HoldenLab/microscope-incubation-box/Individual_parts/R2_door.dxf

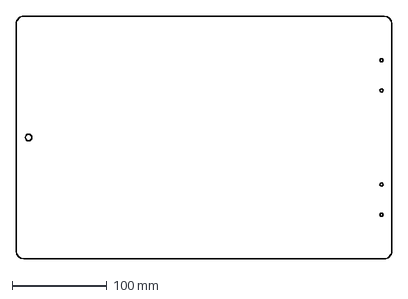
[picture p3: CAD file, 2018-10-10]
Individual_parts/R2_door.dxf
396.0 x 256.0 mm
