HoldenLab/microscope-incubation-box/Individual_parts/PDFs/F6_top_door_hinges_2spacers.pdf

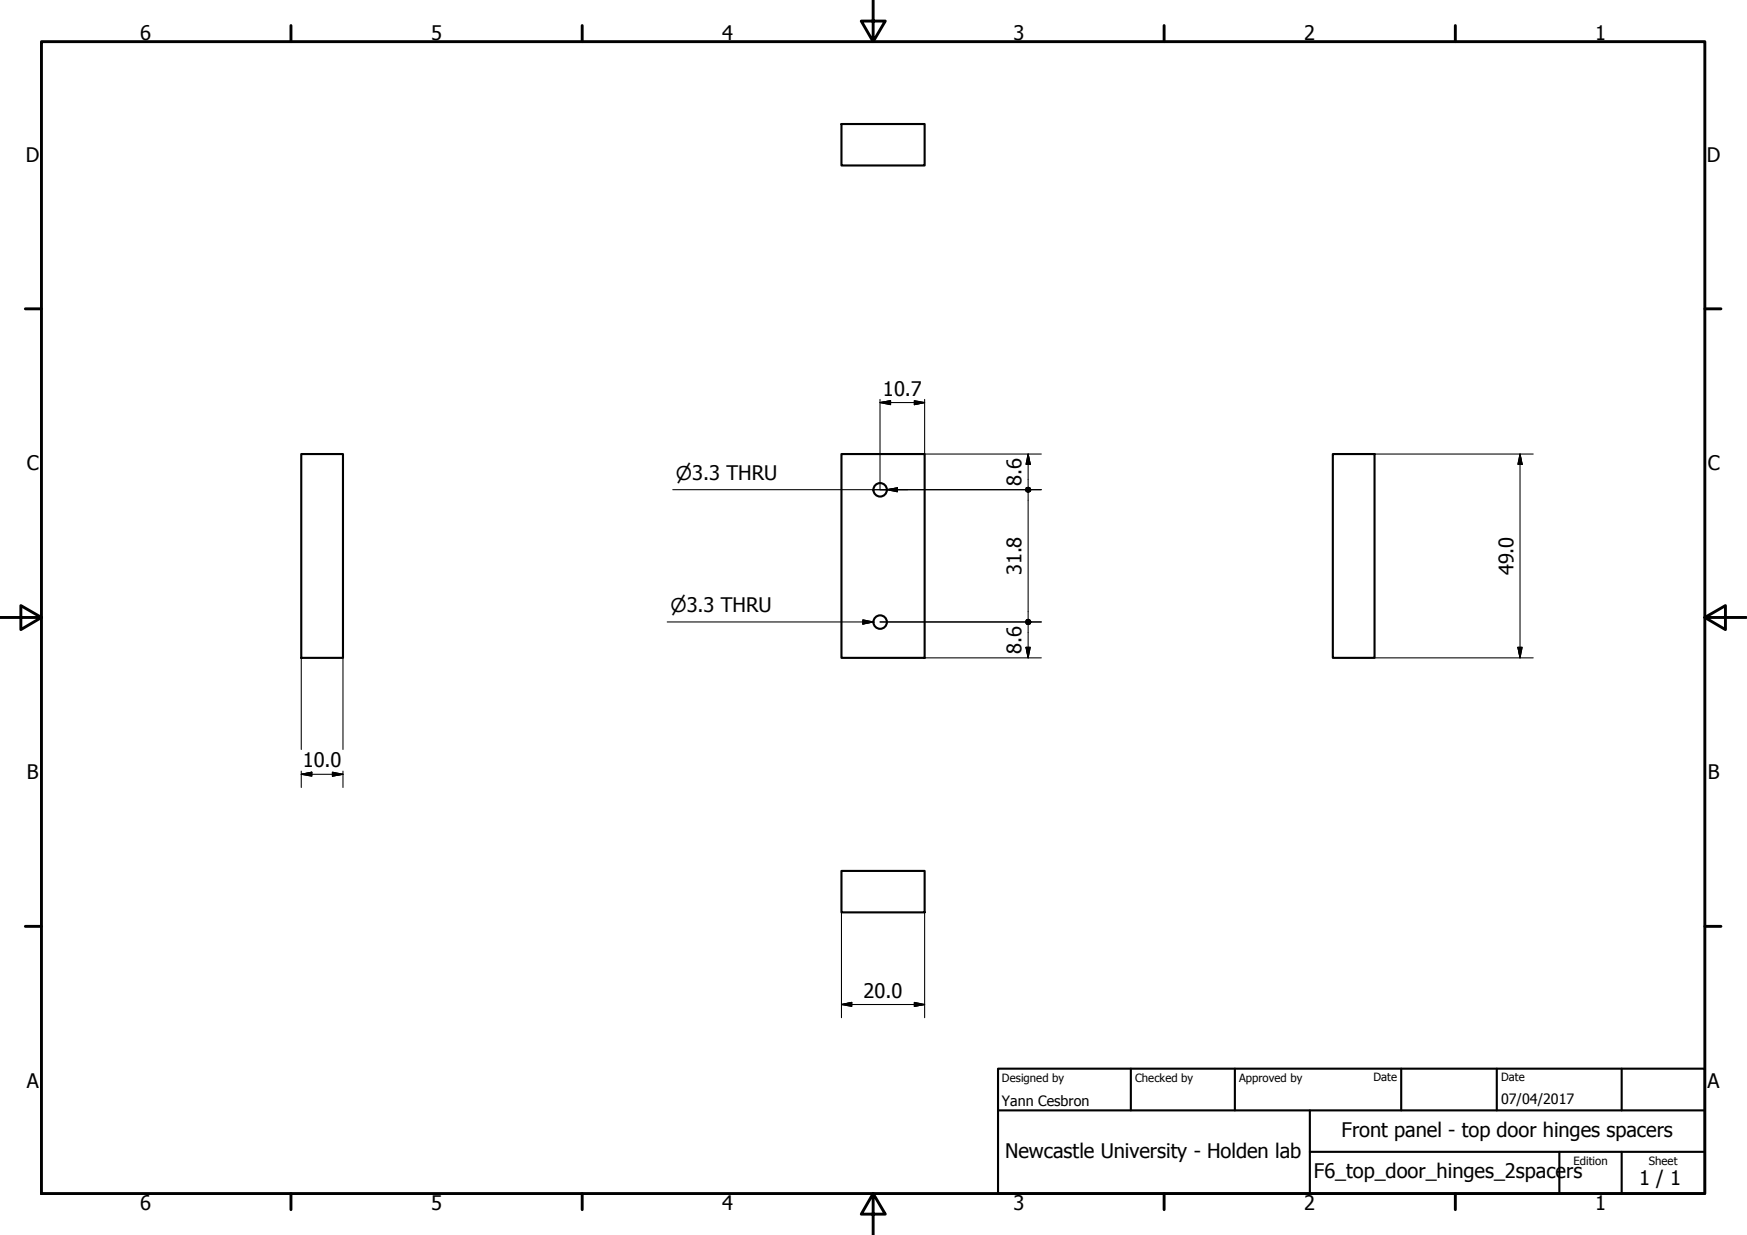
[picture p10: page 1]
F6_top_door_hinges_2spacers; Yann Cesbron; Designed by; Checked by; Approved by; Date; Edition; Sheet; P3.3 THRU

Front panel - top door hinges spacers

Newcastle University - Holden lab
