HoldenLab/microscope-incubation-box/Individual_parts/PDFs/L8_door_magnet_flange.pdf

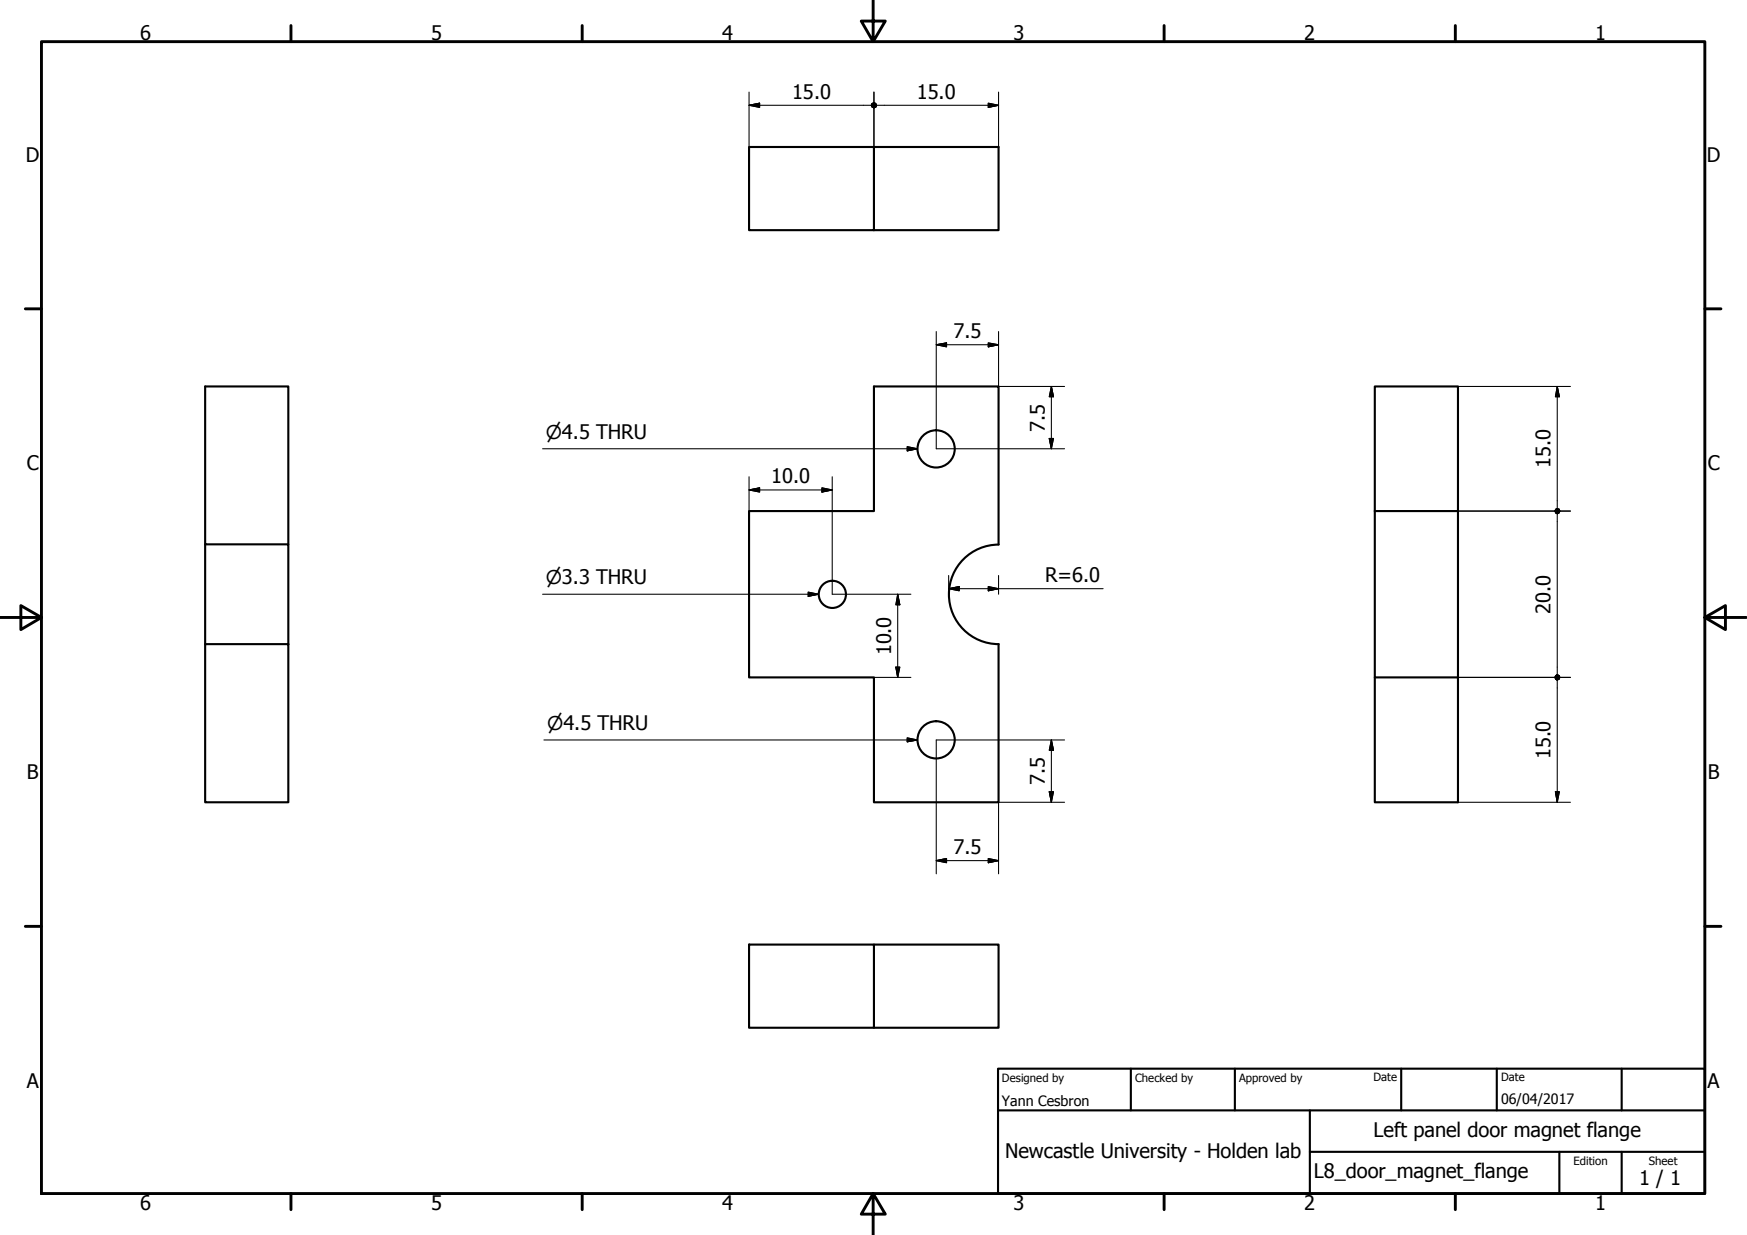
[picture p11: page 1]
L8_door_magnet_flange; Yann Cesbron; Designed by; Checked by; Approved by; Date; Edition; Sheet; P4.5 THRU; P3.3 THRU

Left panel door magnet flange

Newcastle University - Holden lab
