HoldenLab/microscope-incubation-box/Individual_parts/PDFs/R3_CRISP_flange.pdf

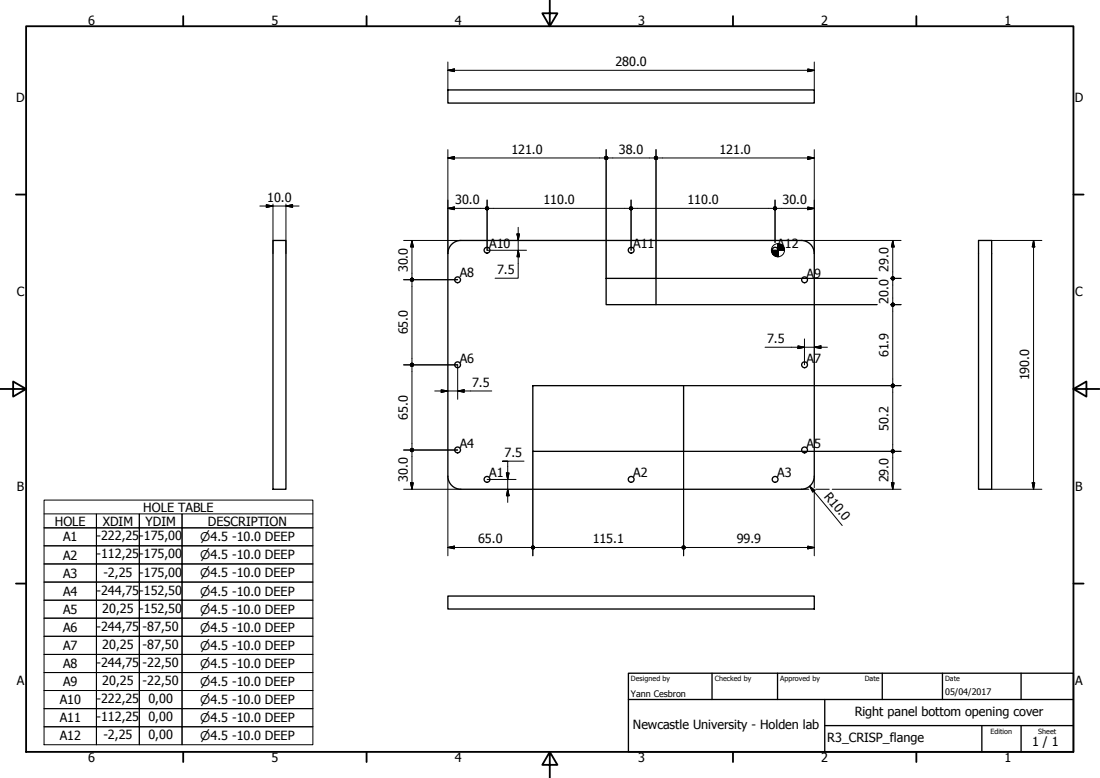
[picture p12: page 1]
R3_CRISP_flange; Yann Cesbron; Designed by; Checked by; Approved by; Date; Edition; Sheet; HOLE TABLE; HOLE; XDIM YDIM; DESCRIPTION; P4.5 -10.0 DEEP

Right panel bottom opening cover

Newcastle University - Holden lab
