HoldenLab/microscope-incubation-box/Individual_parts/PDFs/R8_door_magnet_flange.pdf

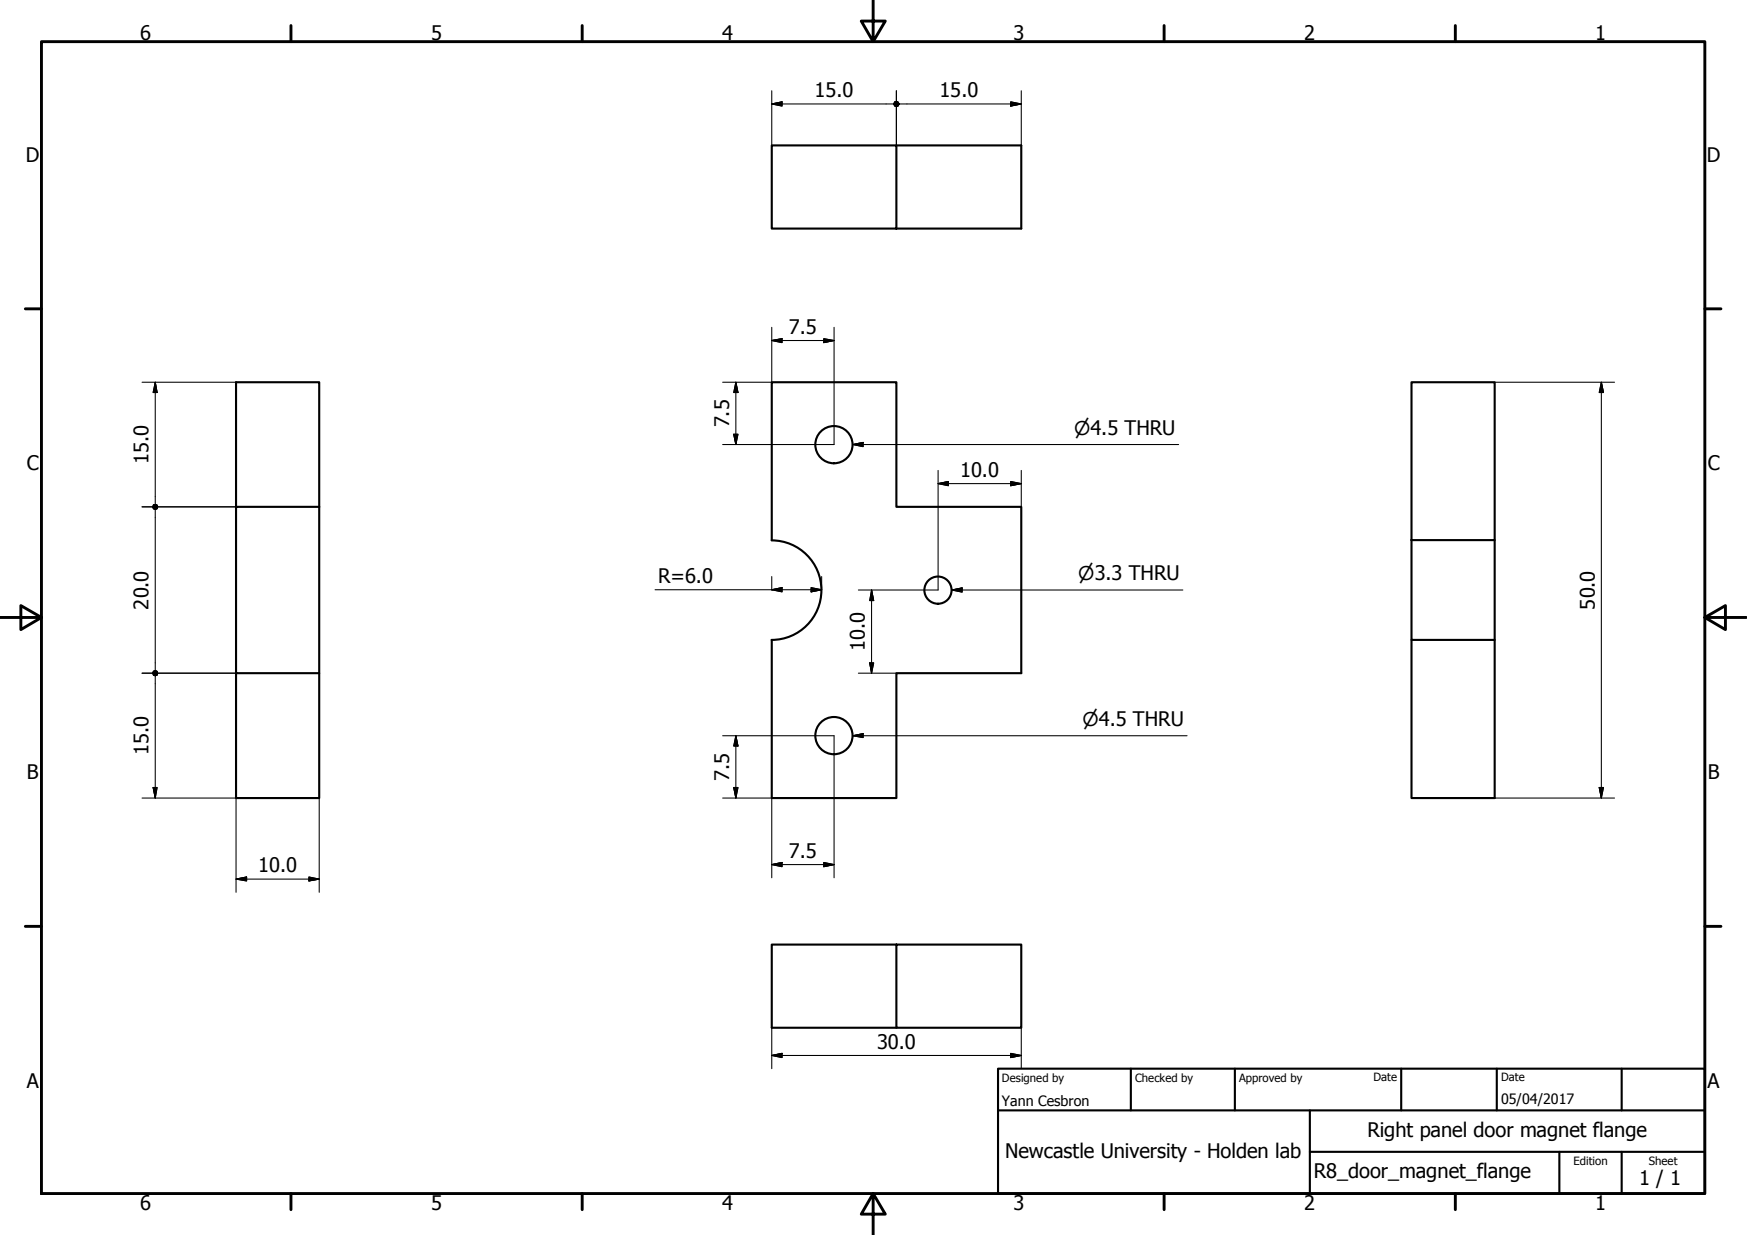
[picture p13: page 1]
R8_door_magnet_flange; Yann Cesbron; Designed by; Checked by; Approved by; Date; Edition; Sheet; P4.5 THRU; P3.3 THRU

Right panel door magnet flange

Newcastle University - Holden lab
