HoldenLab/microscope-incubation-box/Individual_parts/PDFs/T3_flanges.pdf

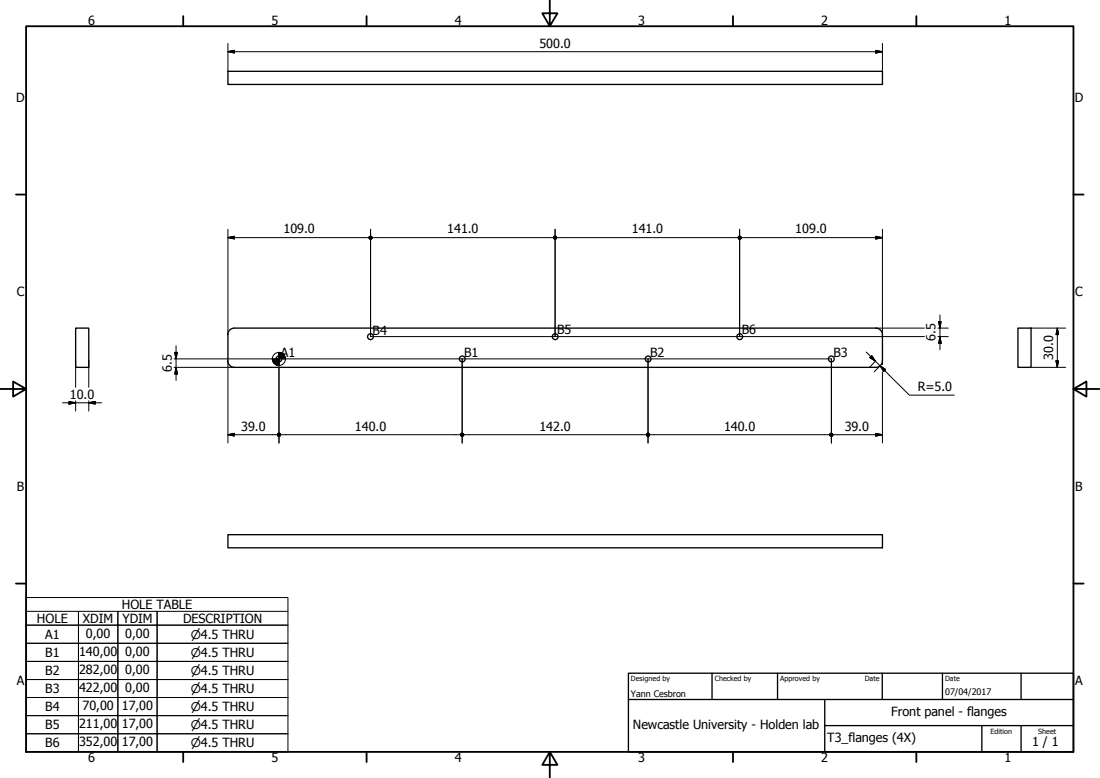
[picture p14: page 1]
T3_flanges (4X); Yann Cesbron; Designed by; Checked by; Approved by; Date; Edition; Sheet; HOLE TABLE; HOLE; XDIM YDIM; DESCRIPTION; P4.5 THRU

Front panel - flanges

Newcastle University - Holden lab
