HoldenLab/microscope-incubation-box/Individual_parts/PDFs/Missing_holes/L1_main.pdf

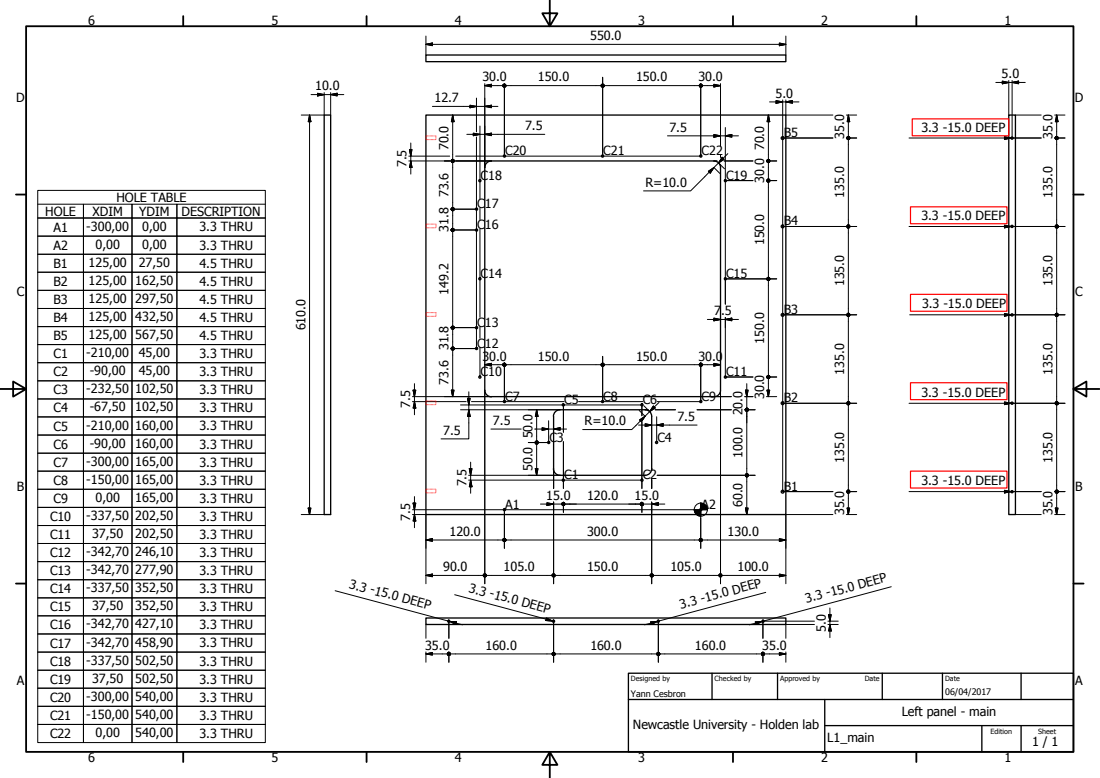
[picture p15: page 1]

HOLE XDIM YDIM DESCRIPTION

Newcastle University - Holden lab
