HoldenLab/microscope-incubation-box/Individual_parts/PDFs/F1_main.pdf

P

P

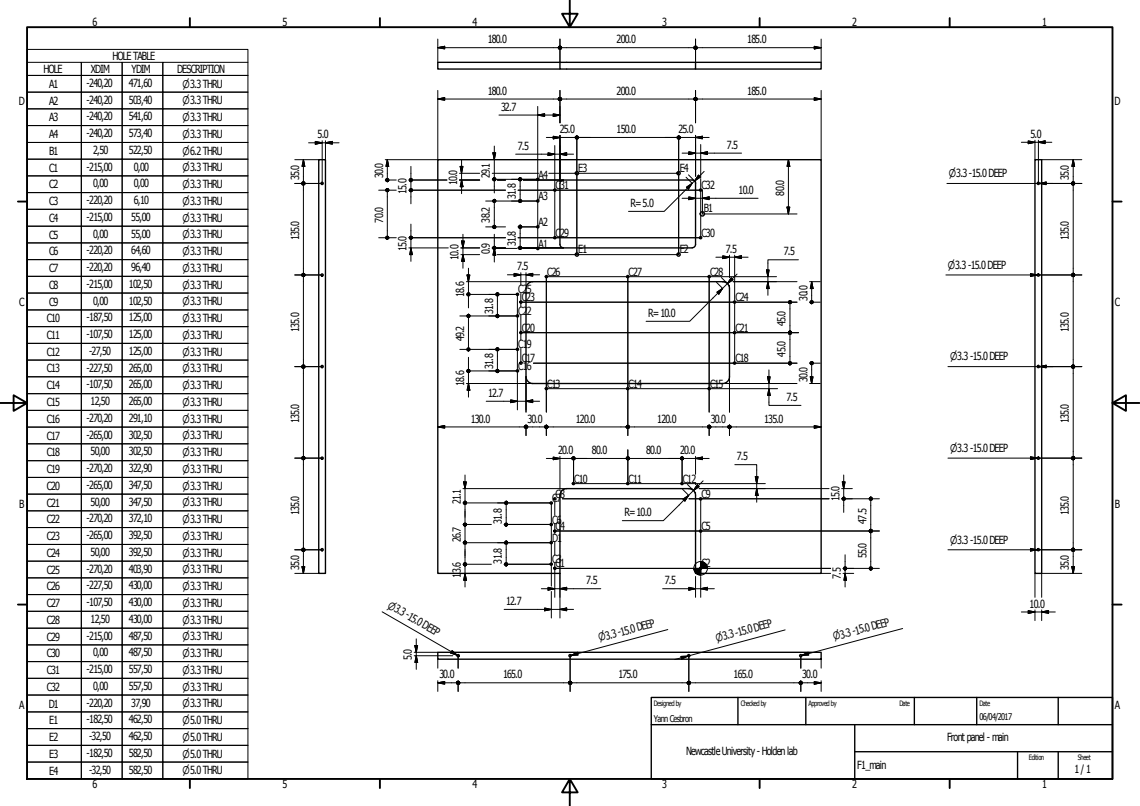
[picture p22: page 1]

E3 | C3 2
C3
