HoldenLab/microscope-incubation-box/Individual_parts/PDFs/F2_top_door.pdf

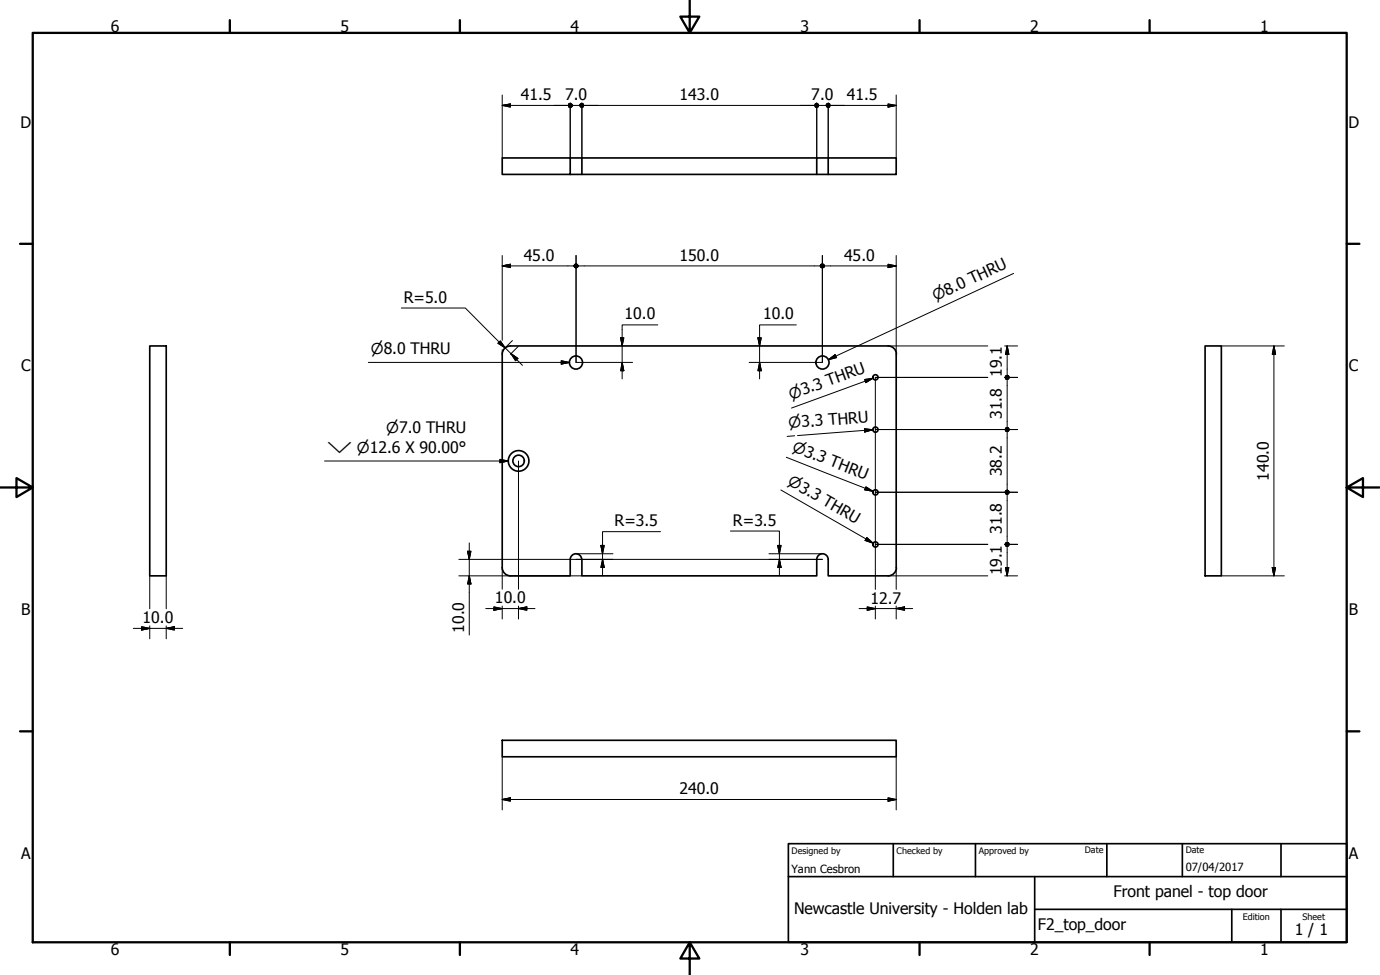
[picture p23: page 1]
F2_top_door; Yann Cesbron; Designed by; Checked by; Approved by; Date; Edition; Sheet; P7.0 THRU Y P12.6 X 90.00°; P8.0 THRU; P3.3 THRU; P3.3 THRU P3.3 THRU

Front panel - top door

Newcastle University - Holden lab
