HoldenLab/microscope-incubation-box/Individual_parts/PDFs/F3_middle_door.pdf

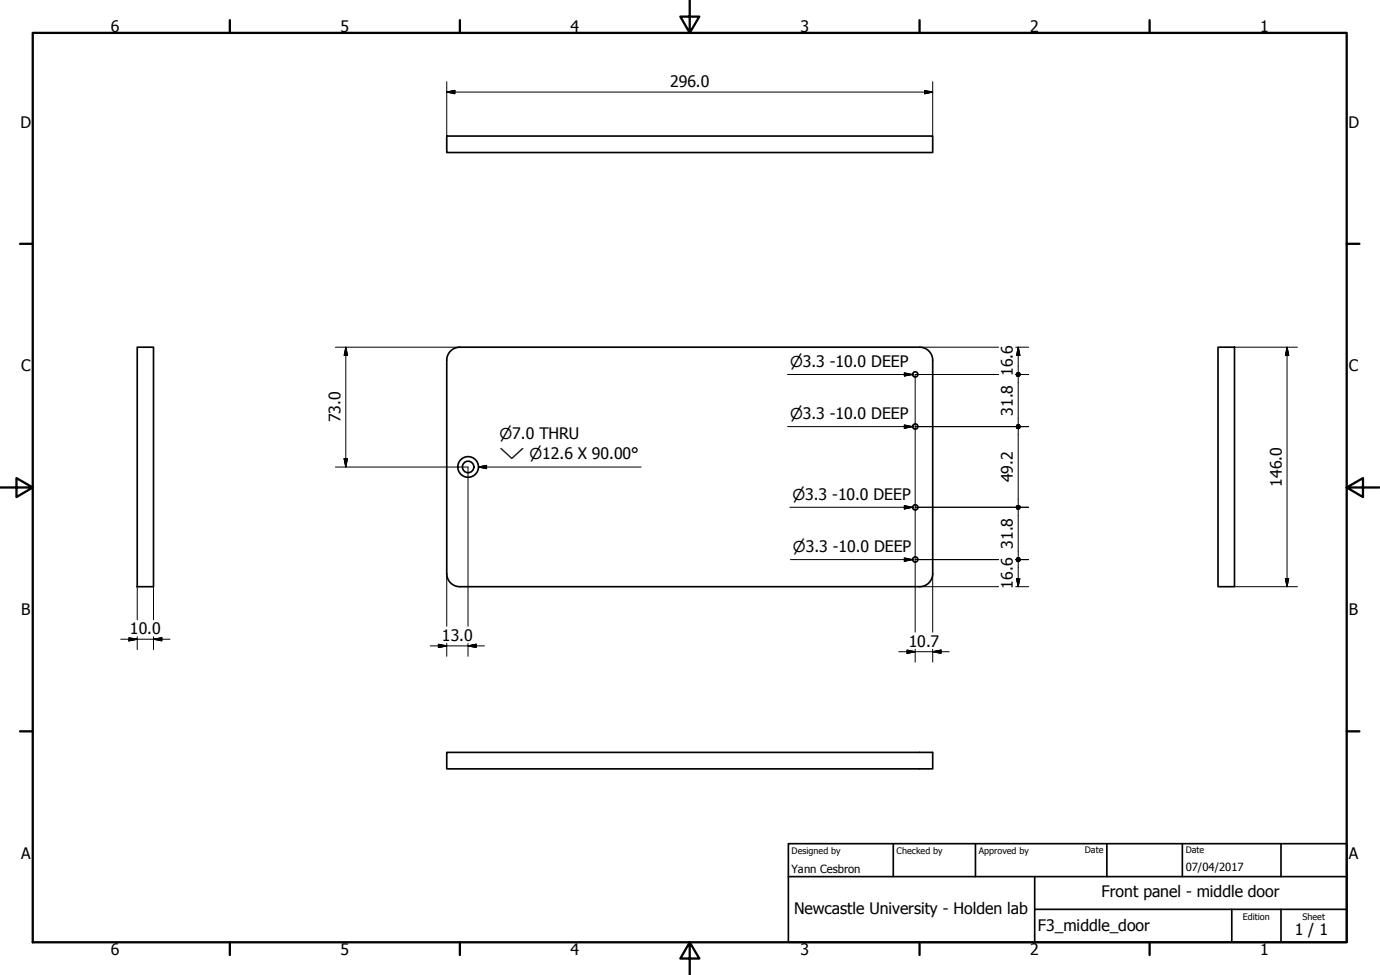
[picture p24: page 1]
F3_middle_door; Yann Cesbron; Designed by; Checked by; Approved by; Date; Edition; Sheet; P3.3 -10.0 DEEP; P7.0 THRU Y P12.6 X 90.00°

Front panel - middle door

Newcastle University - Holden lab
