HoldenLab/microscope-incubation-box/Individual_parts/PDFs/F4_bottom_door.pdf

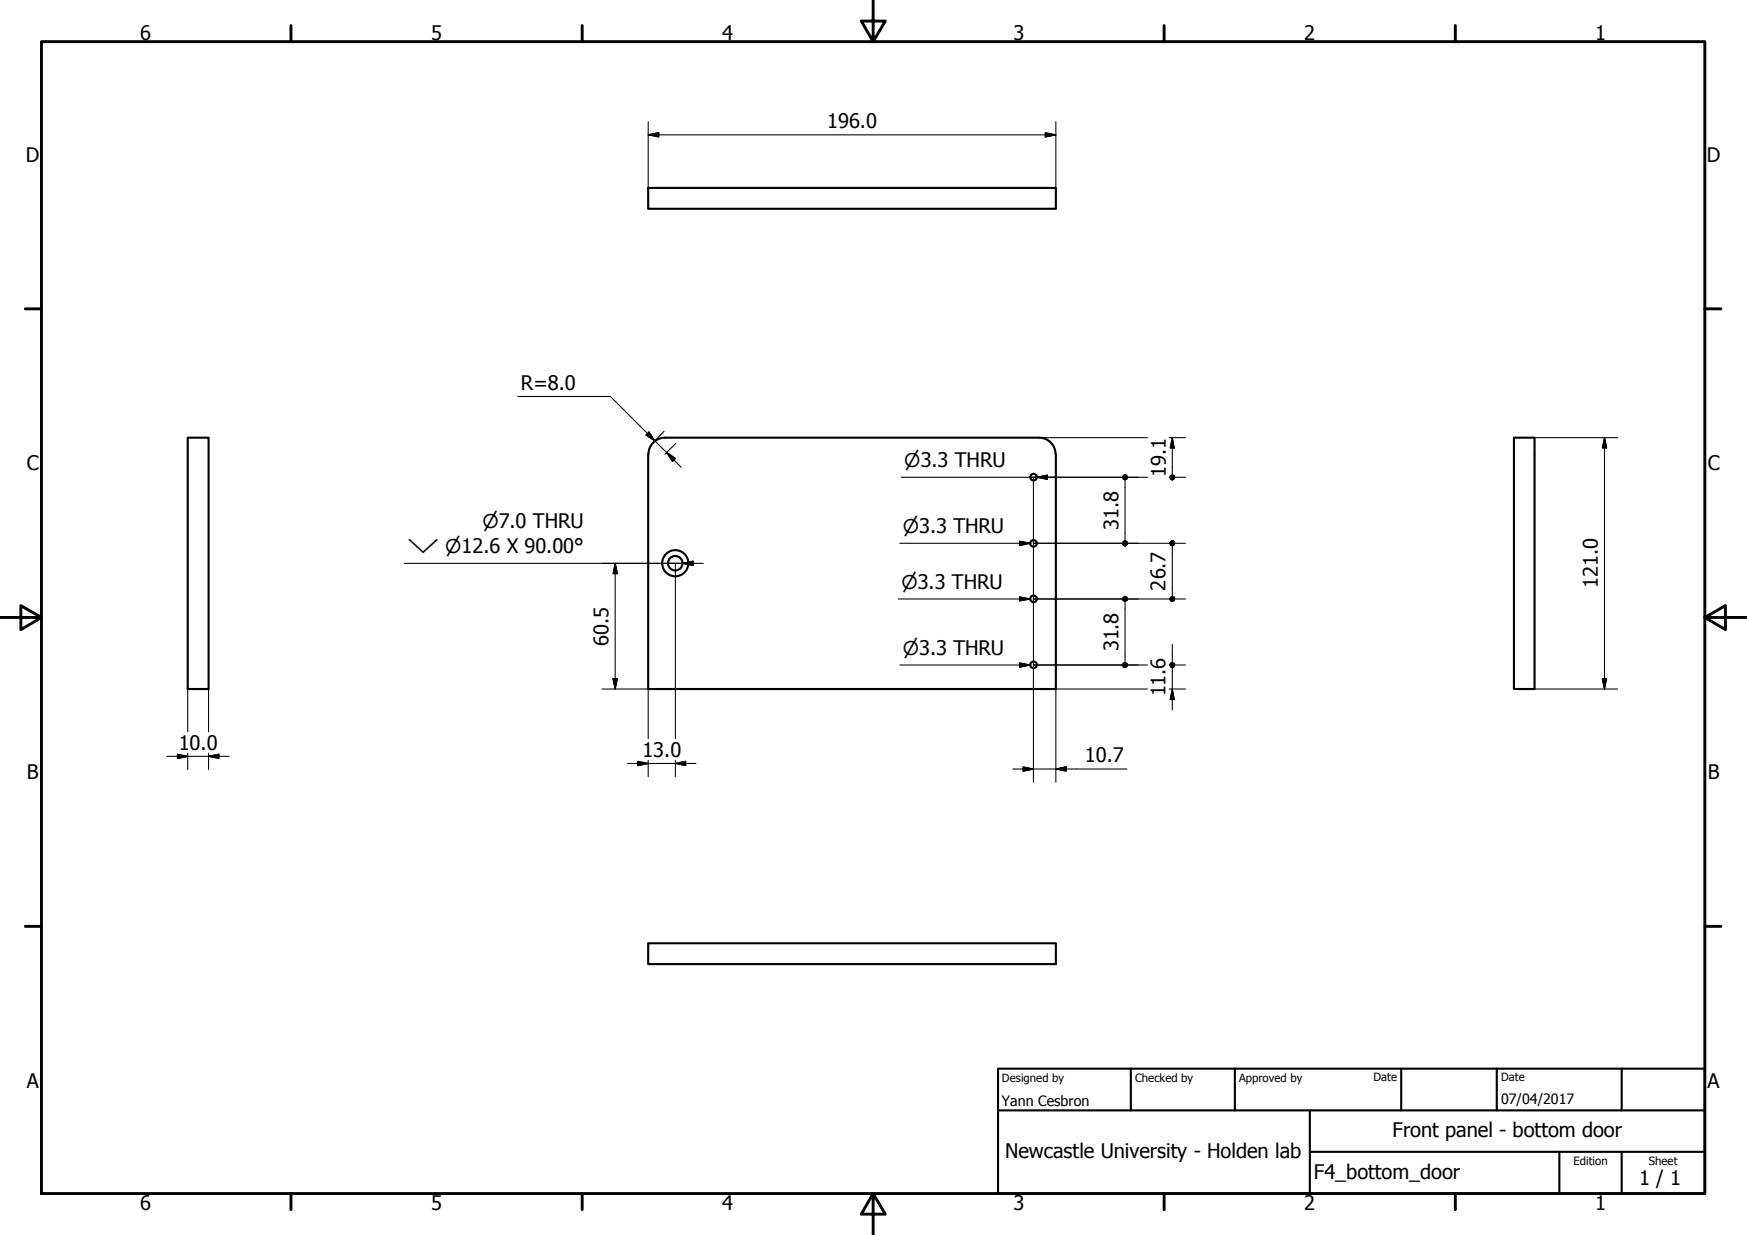
[picture p25: page 1]
F4_bottom_door; Yann Cesbron; Designed by; Checked by; Approved by; Date; Edition; Sheet; P3.3 THRU; P7.0 THRU Y P12.6 X 90.00°

Front panel - bottom door

Newcastle University - Holden lab
