HoldenLab/microscope-incubation-box/Individual_parts/PDFs/F5_top_door_window.pdf

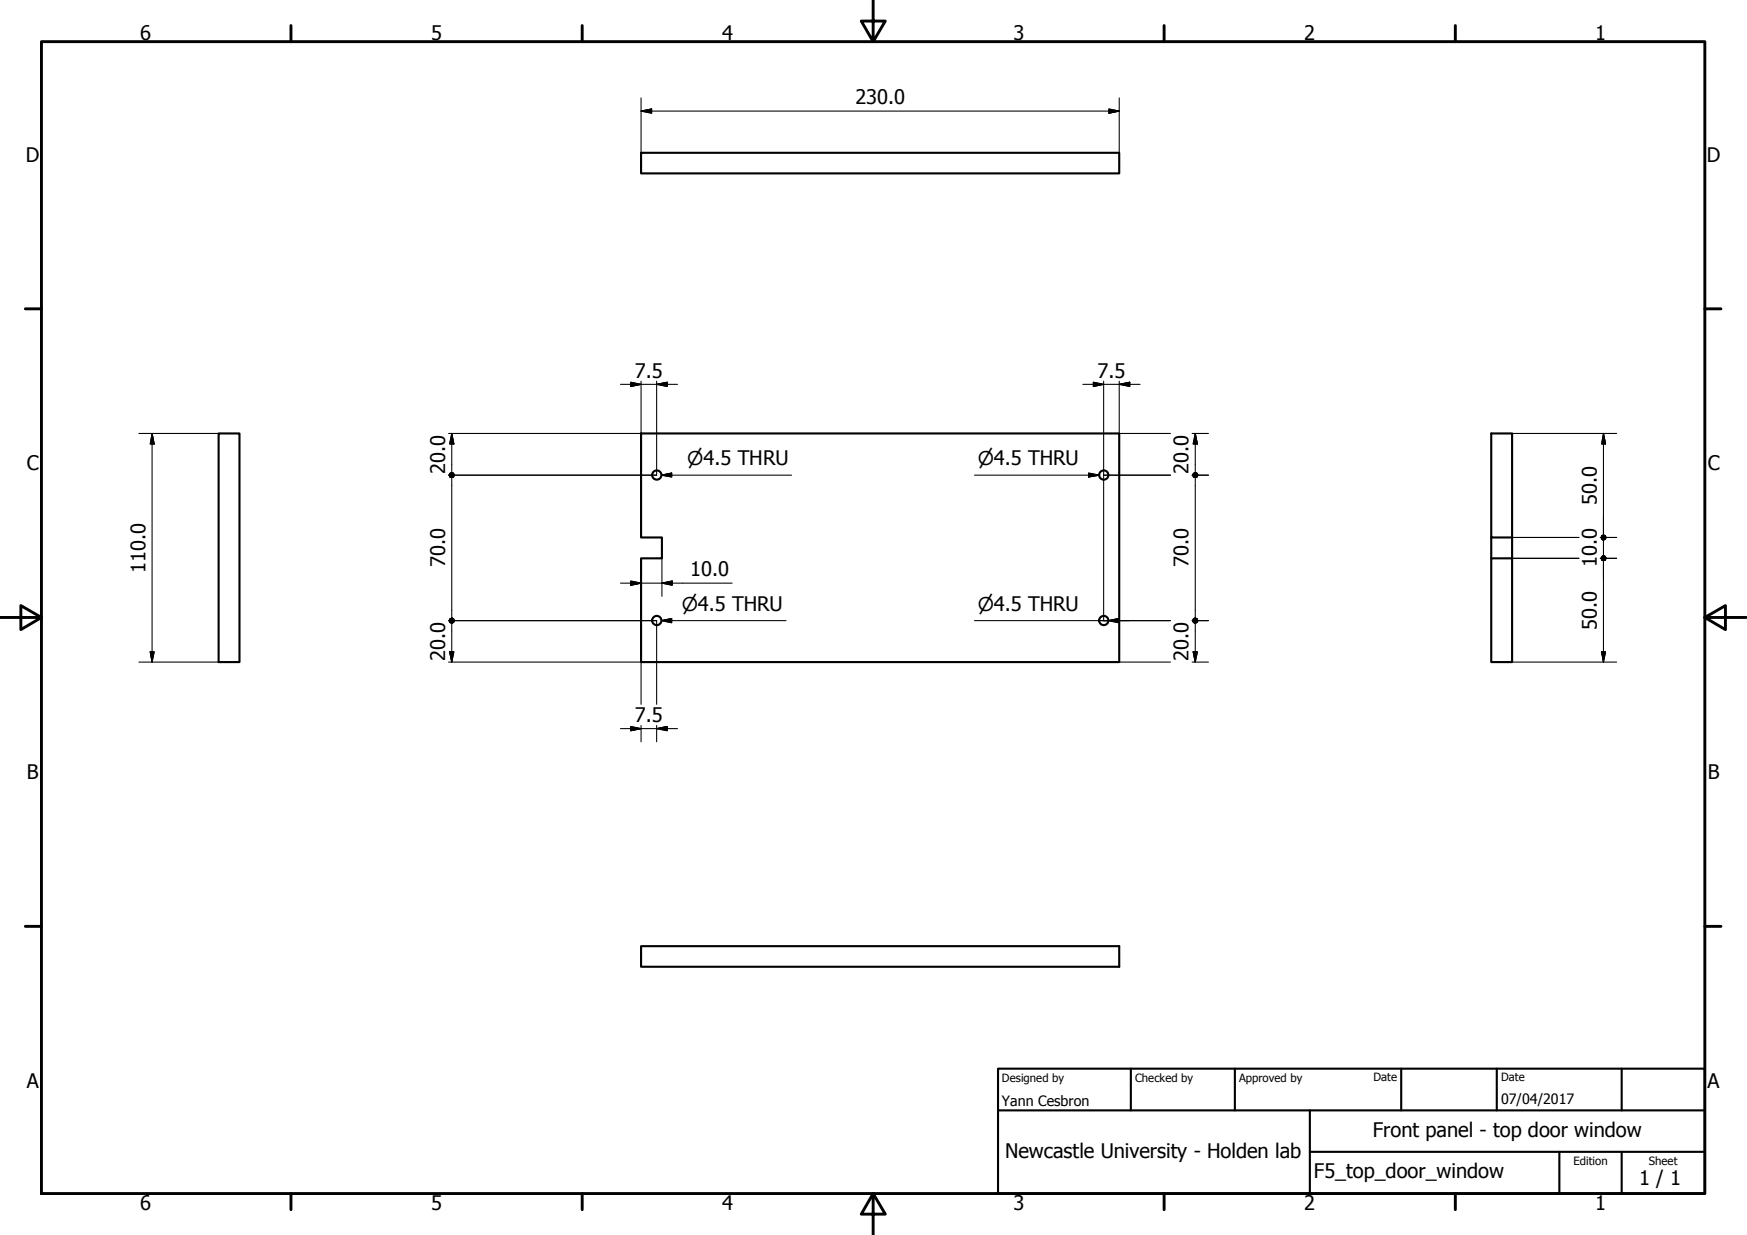
[picture p26: page 1]
F5_top_door_window; Yann Cesbron; Designed by; Checked by; Approved by; Date; Edition; Sheet; P4.5 THRU

Front panel - top door window

Newcastle University - Holden lab
