HoldenLab/microscope-incubation-box/Individual_parts/PDFs/F7_middle_door_left_flange_1.pdf

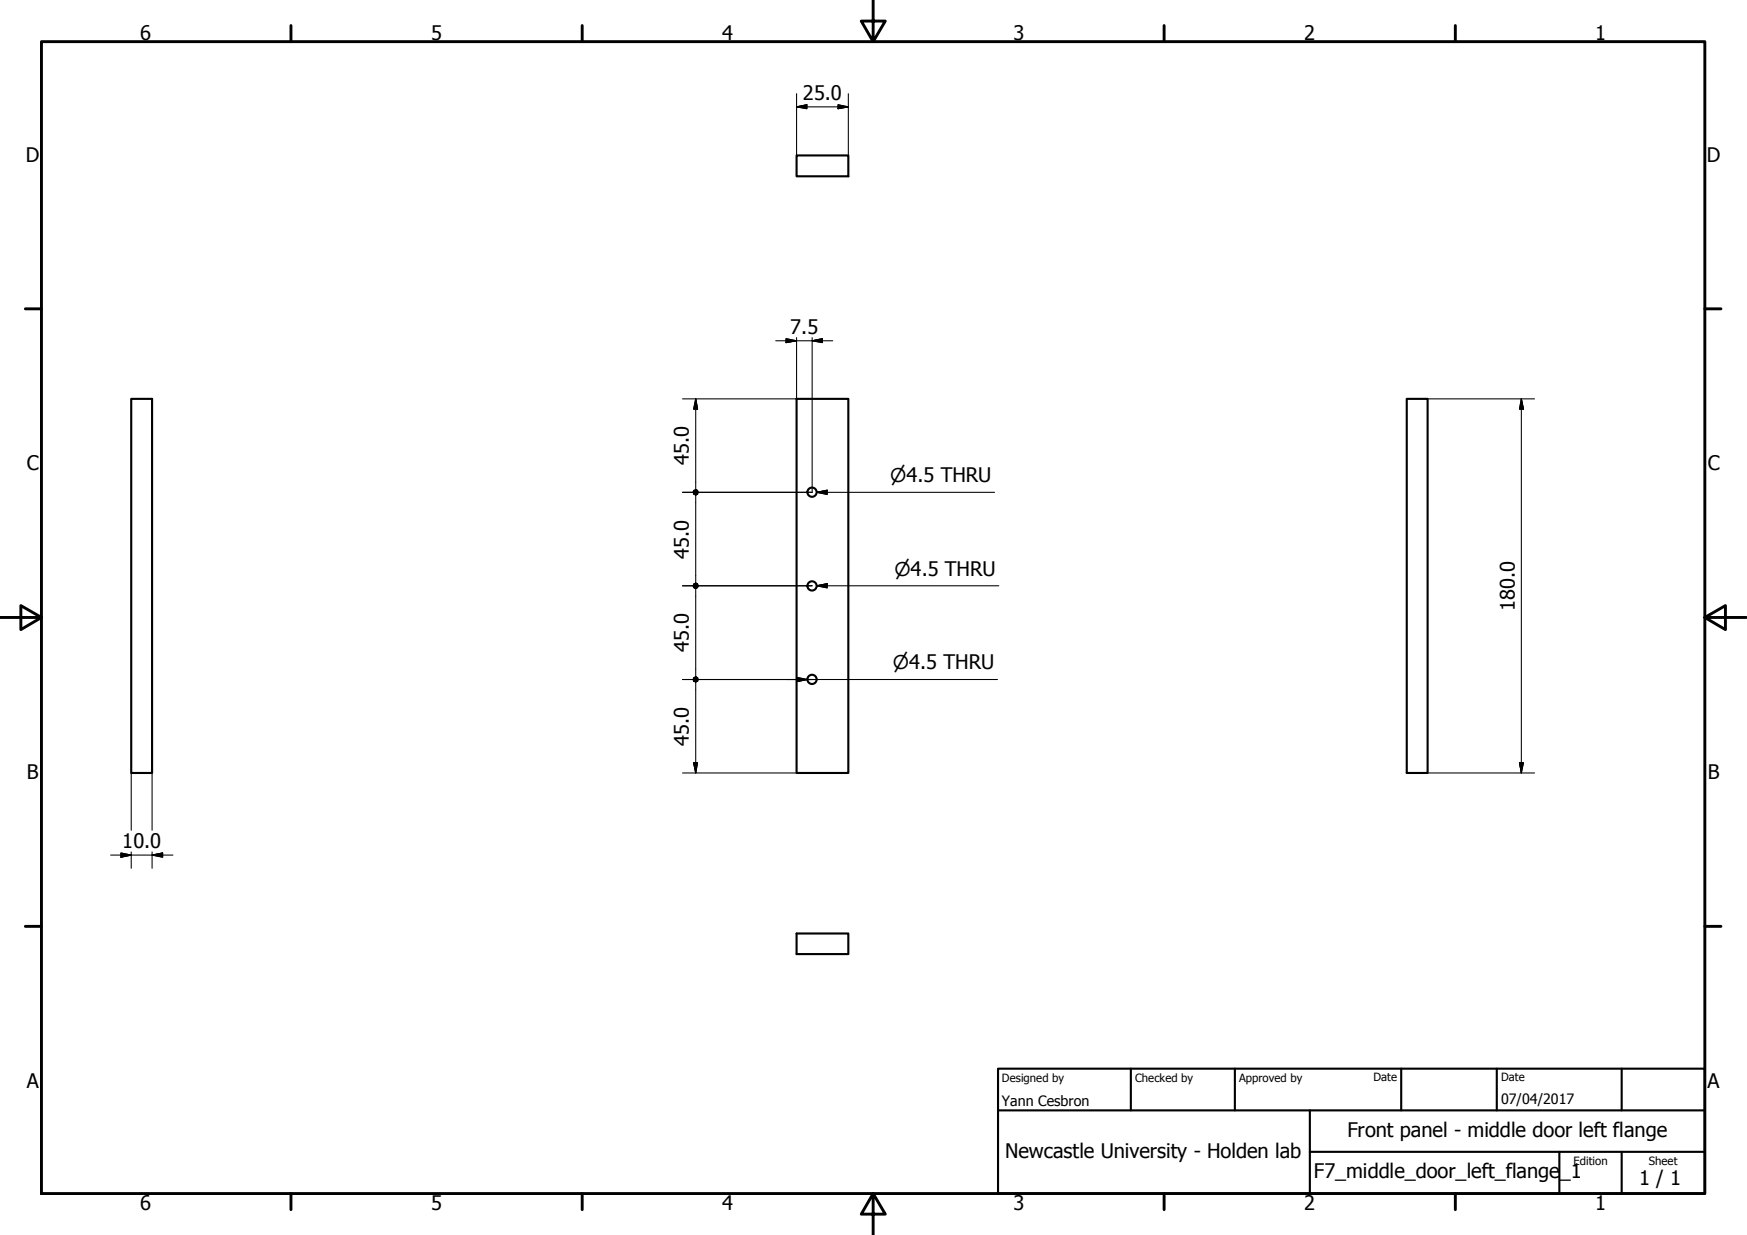
[picture p27: page 1]
F7_middle_door_left_flange_1; Yann Cesbron; Designed by; Checked by; Approved by; Date; Edition; Sheet; P4.5 THRU

Front panel - middle door left flange

Newcastle University - Holden lab
