HoldenLab/microscope-incubation-box/Individual_parts/PDFs/F8_middle_door_right_flange_2.pdf

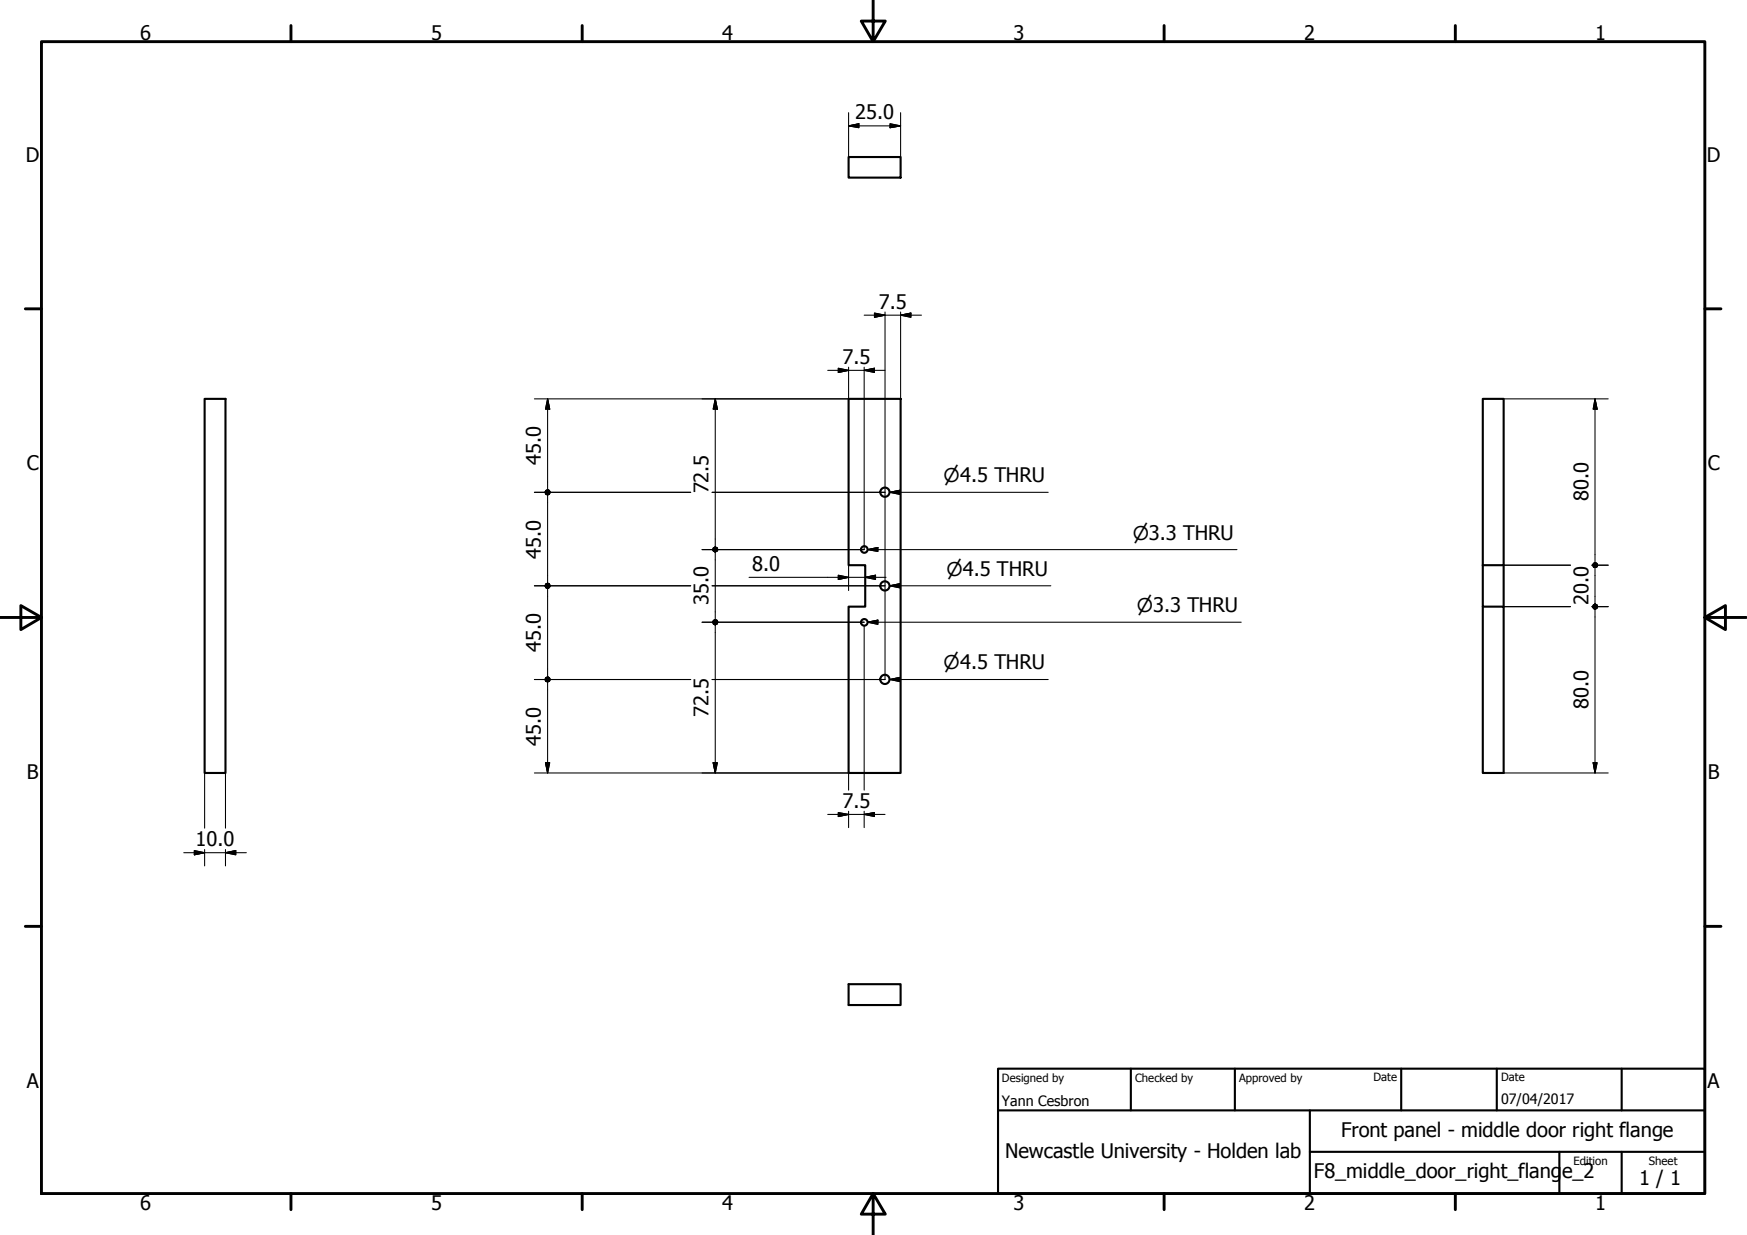
[picture p28: page 1]
F8_middle_door_right_flange_2; Yann Cesbron; Designed by; Checked by; Approved by; Date; Edition; Sheet; P4.5 THRU; P3.3 THRU

Front panel - middle door right flange

Newcastle University - Holden lab
