HoldenLab/microscope-incubation-box/Individual_parts/PDFs/F9_middle_door_bottom_flange_3.pdf

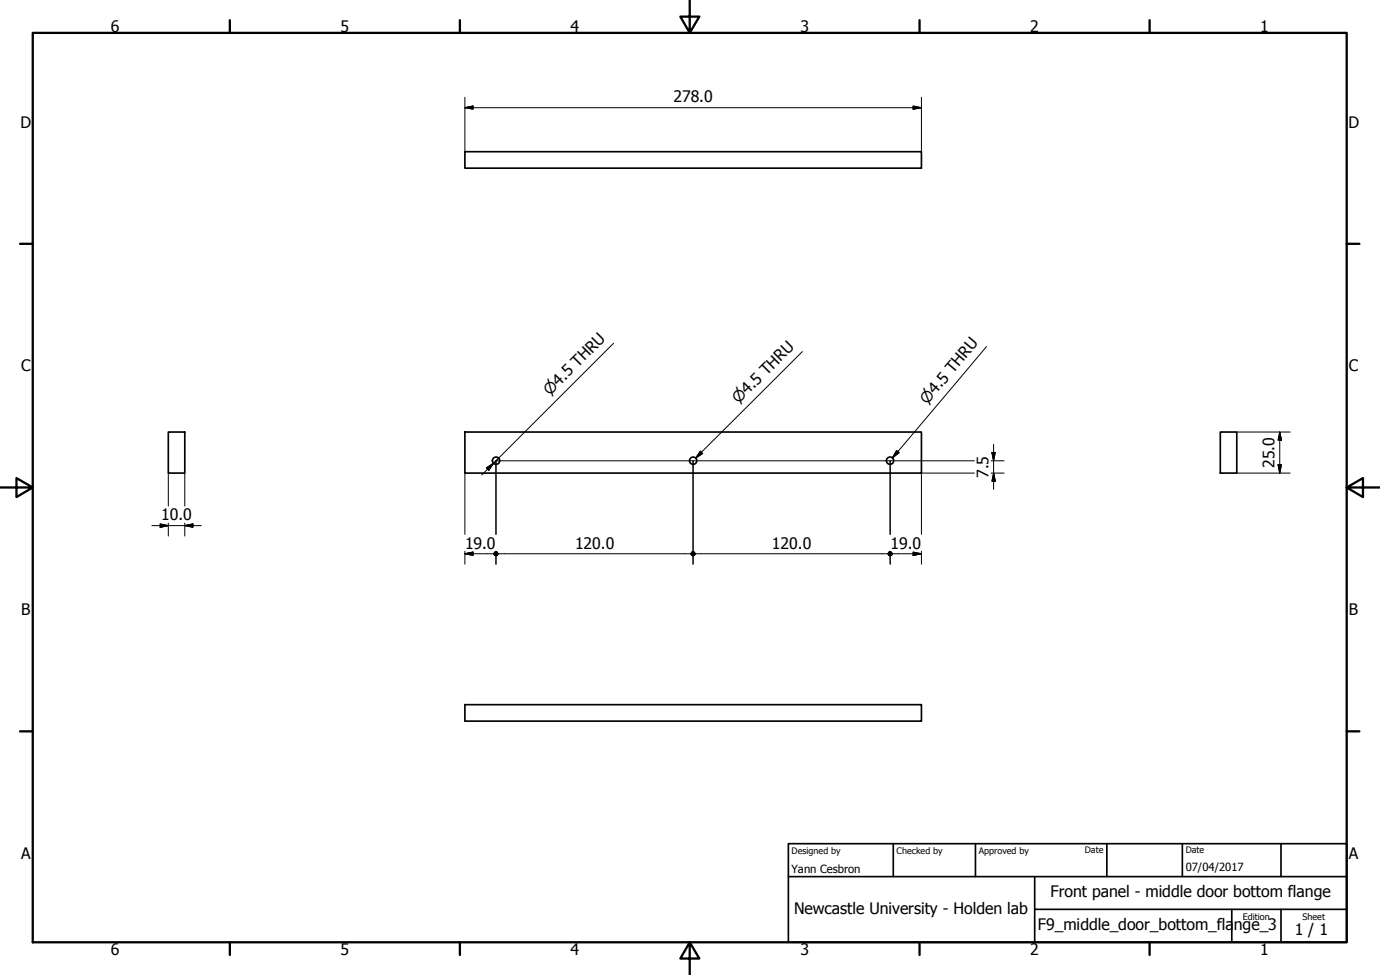
[picture p29: page 1]
F9_middle_door_bottom_flange_3; Yann Cesbron; Designed by; Checked by; Approved by; Date; Edition; Sheet; P4.5 THRU

Front panel - middle door bottom flange

Newcastle University - Holden lab
