HoldenLab/microscope-incubation-box/Individual_parts/PDFs/L1_main.pdf

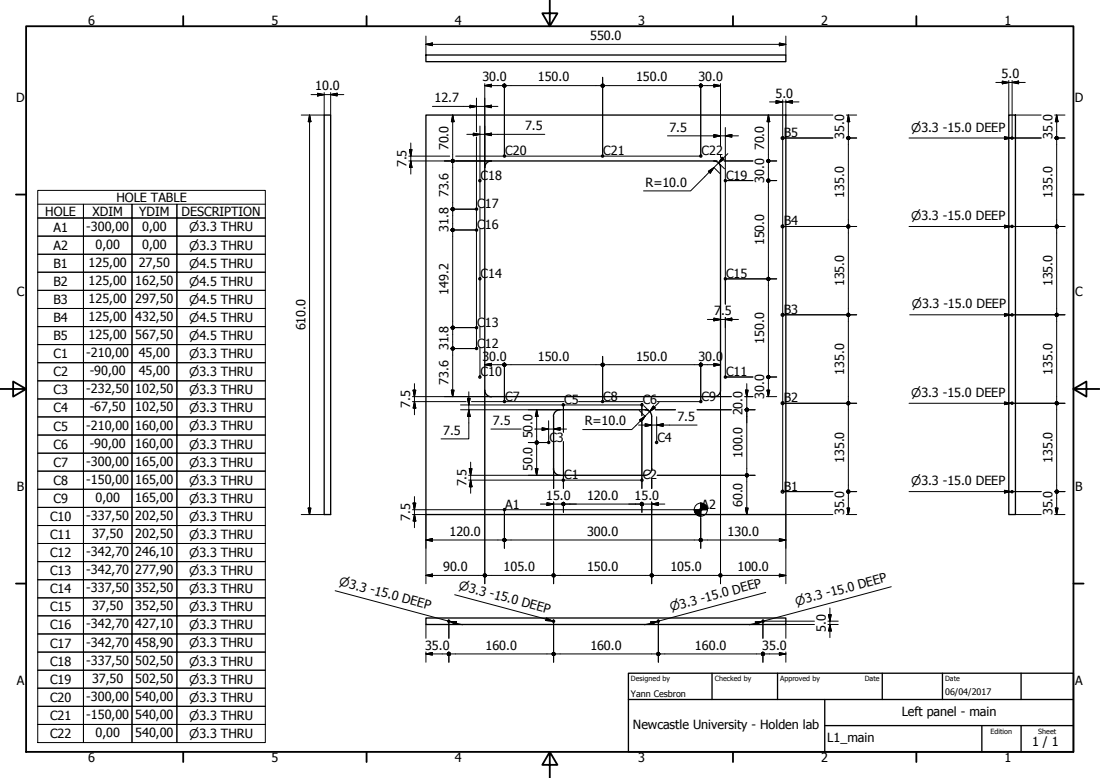
[picture p30: page 1]

Newcastle University - Holden lab
