HoldenLab/microscope-incubation-box/Individual_parts/PDFs/L2_door.pdf

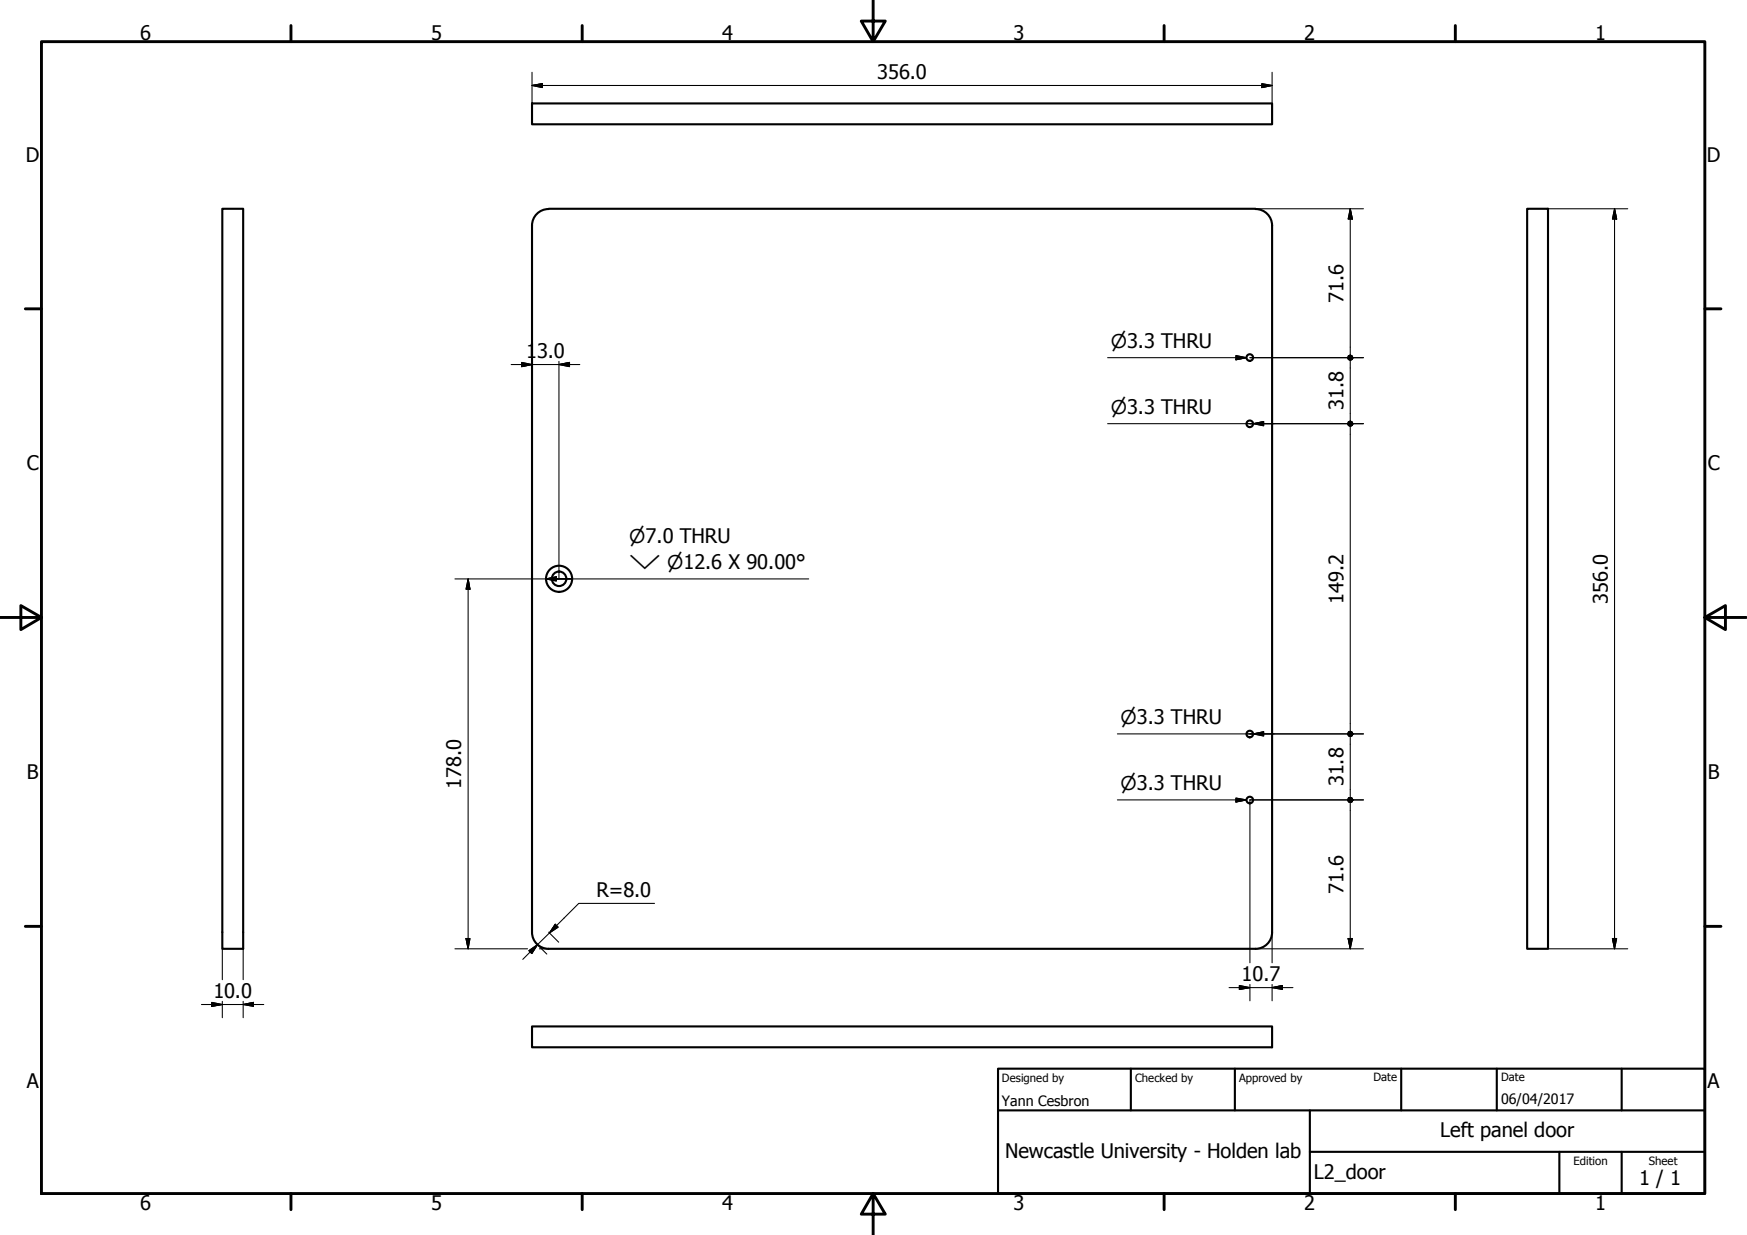
[picture p31: page 1]
L2_door; Yann Cesbron; Designed by; Checked by; Approved by; Date; Edition; Sheet; P7.0 THRU Y P12.6 X 90.00°; P3.3 THRU

Left panel door

Newcastle University - Holden lab
