HoldenLab/microscope-incubation-box/Individual_parts/PDFs/L3_Emission_flange.pdf

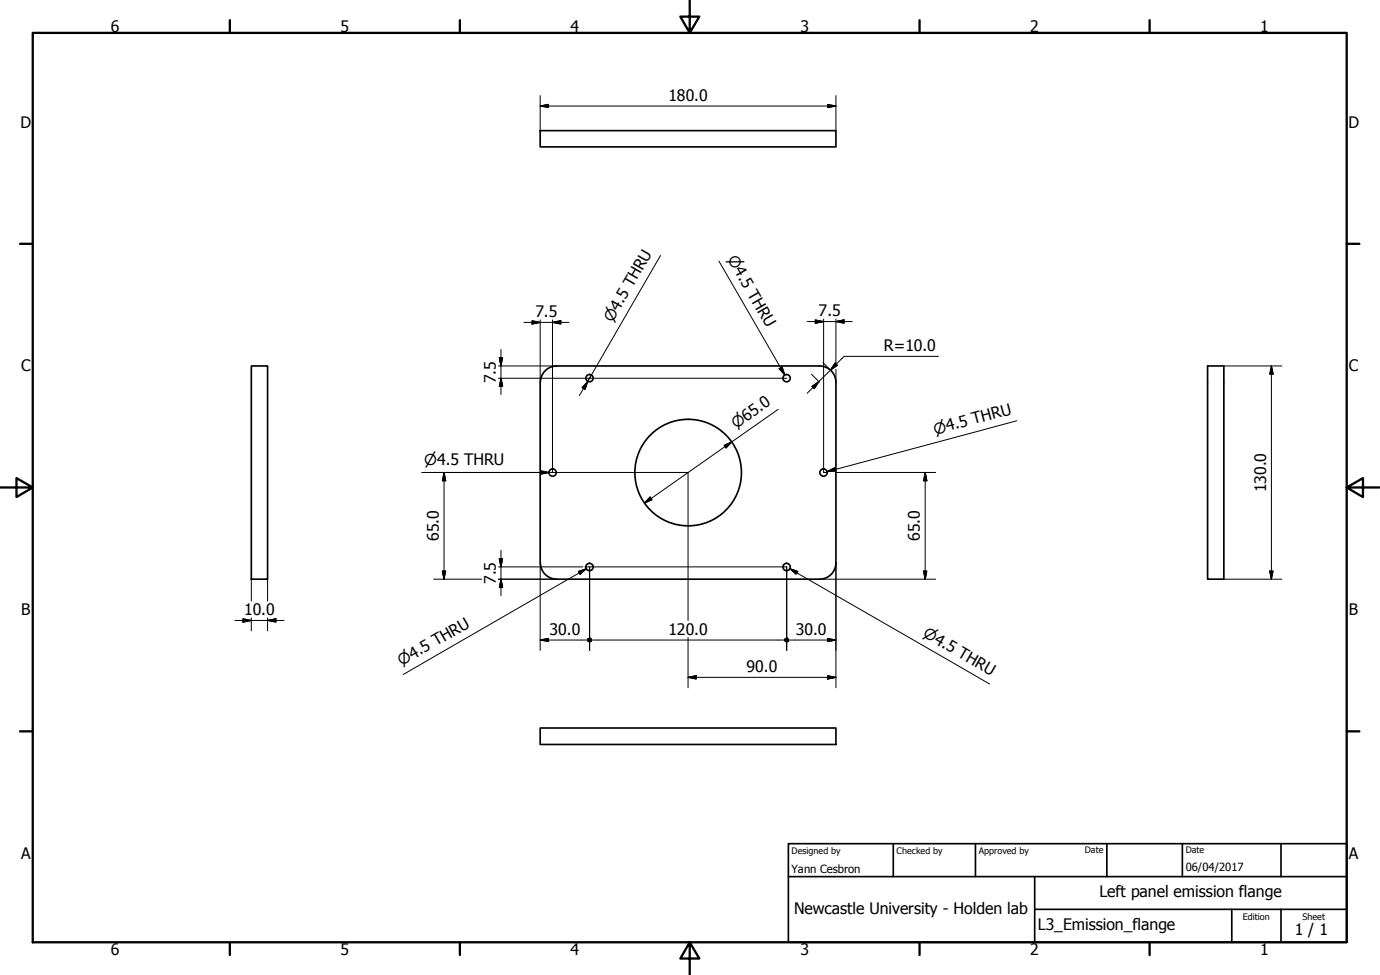
[picture p32: page 1]
L3_Emission_flange; Yann Cesbron; Designed by; Checked by; Approved by; Date; Edition; Sheet; P4.5 THRU

Left panel emission flange

Newcastle University - Holden lab
