HoldenLab/microscope-incubation-box/Individual_parts/PDFs/L4_door_flange_1_left.pdf

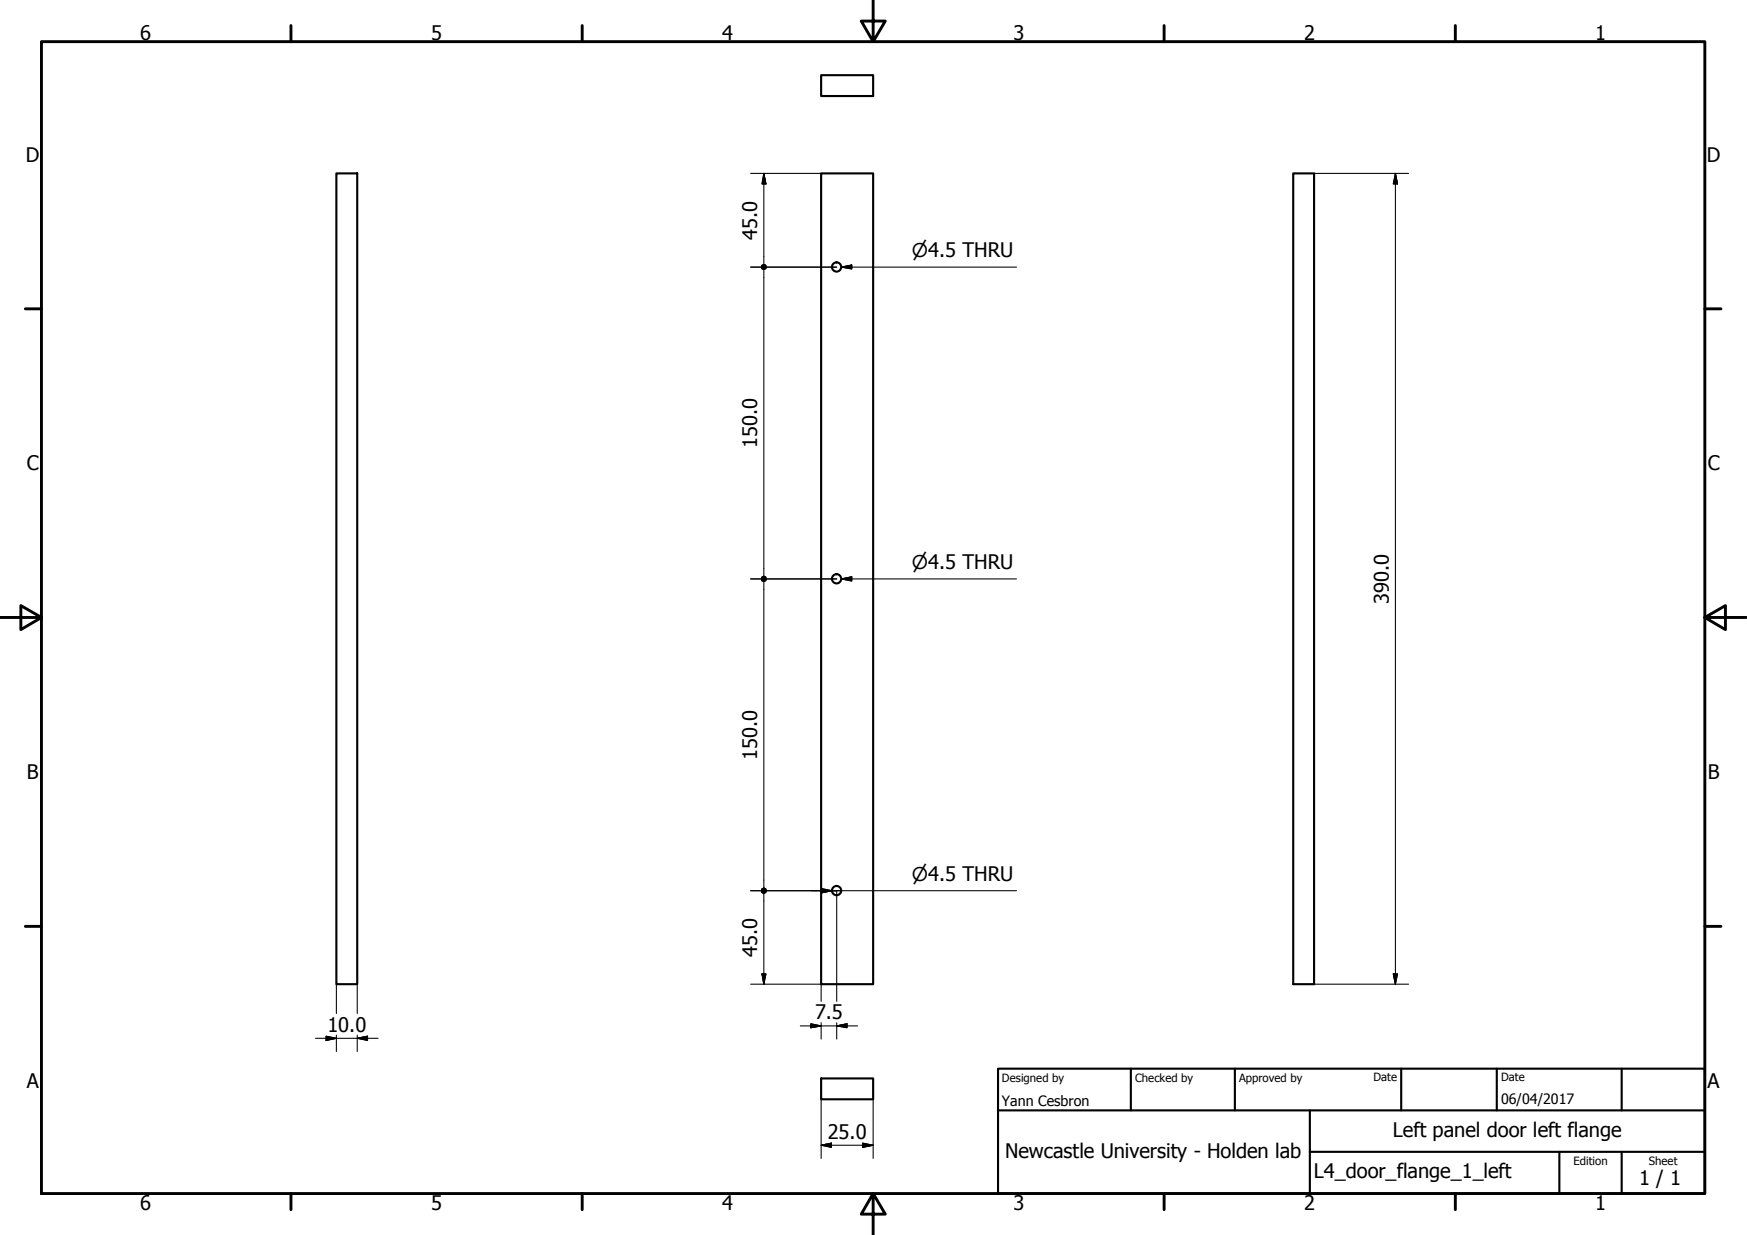
[picture p33: page 1]
L4_door_flange_1_left; Yann Cesbron; Designed by; Checked by; Approved by; Date; Edition; Sheet; P4.5 THRU

Left panel door left flange

Newcastle University - Holden lab
