HoldenLab/microscope-incubation-box/Individual_parts/PDFs/L5_door_flange_2_bottom.pdf

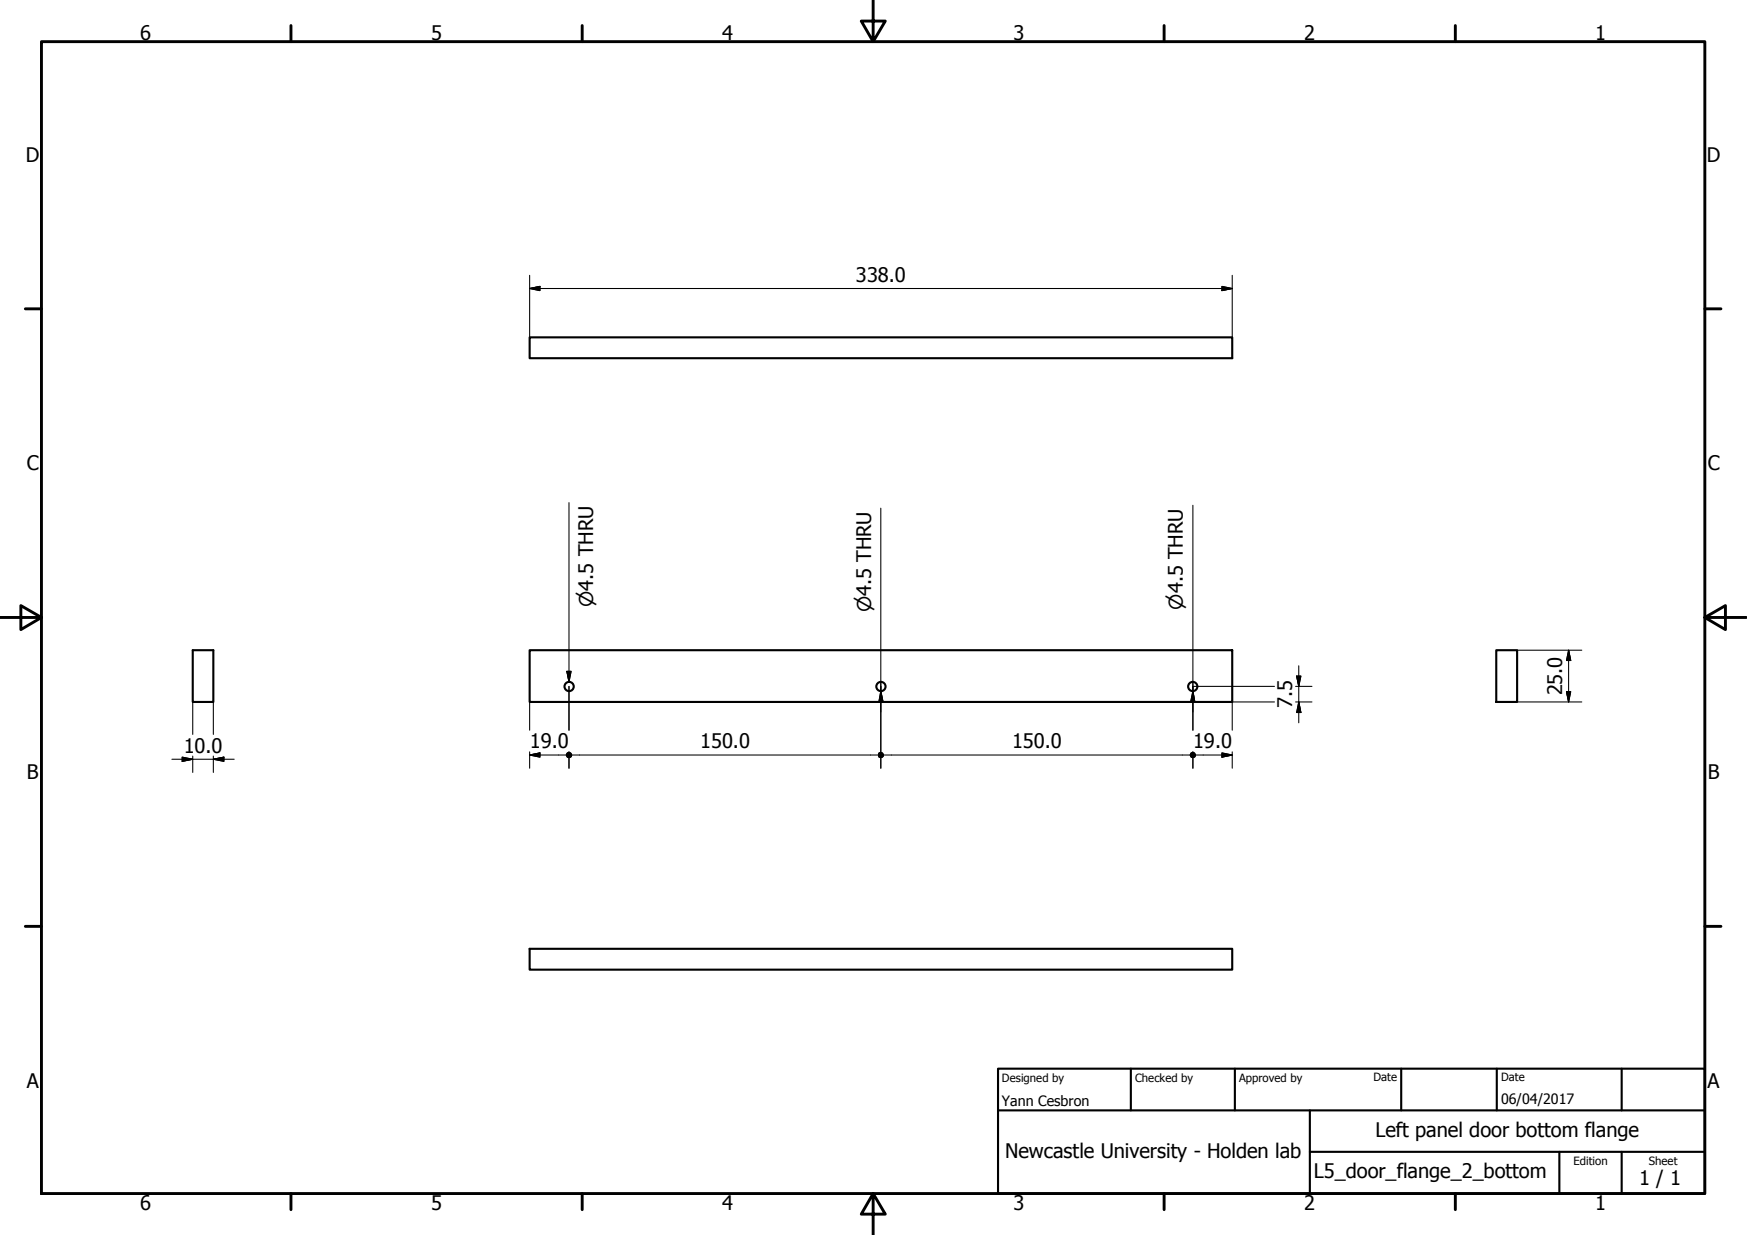
[picture p34: page 1]
L5_door_flange_2_bottom; Yann Cesbron; Designed by; Checked by; Approved by; Date; Edition; Sheet

Left panel door bottom flange

Newcastle University - Holden lab
