HoldenLab/microscope-incubation-box/Individual_parts/PDFs/L6_door_flange_3_top.pdf

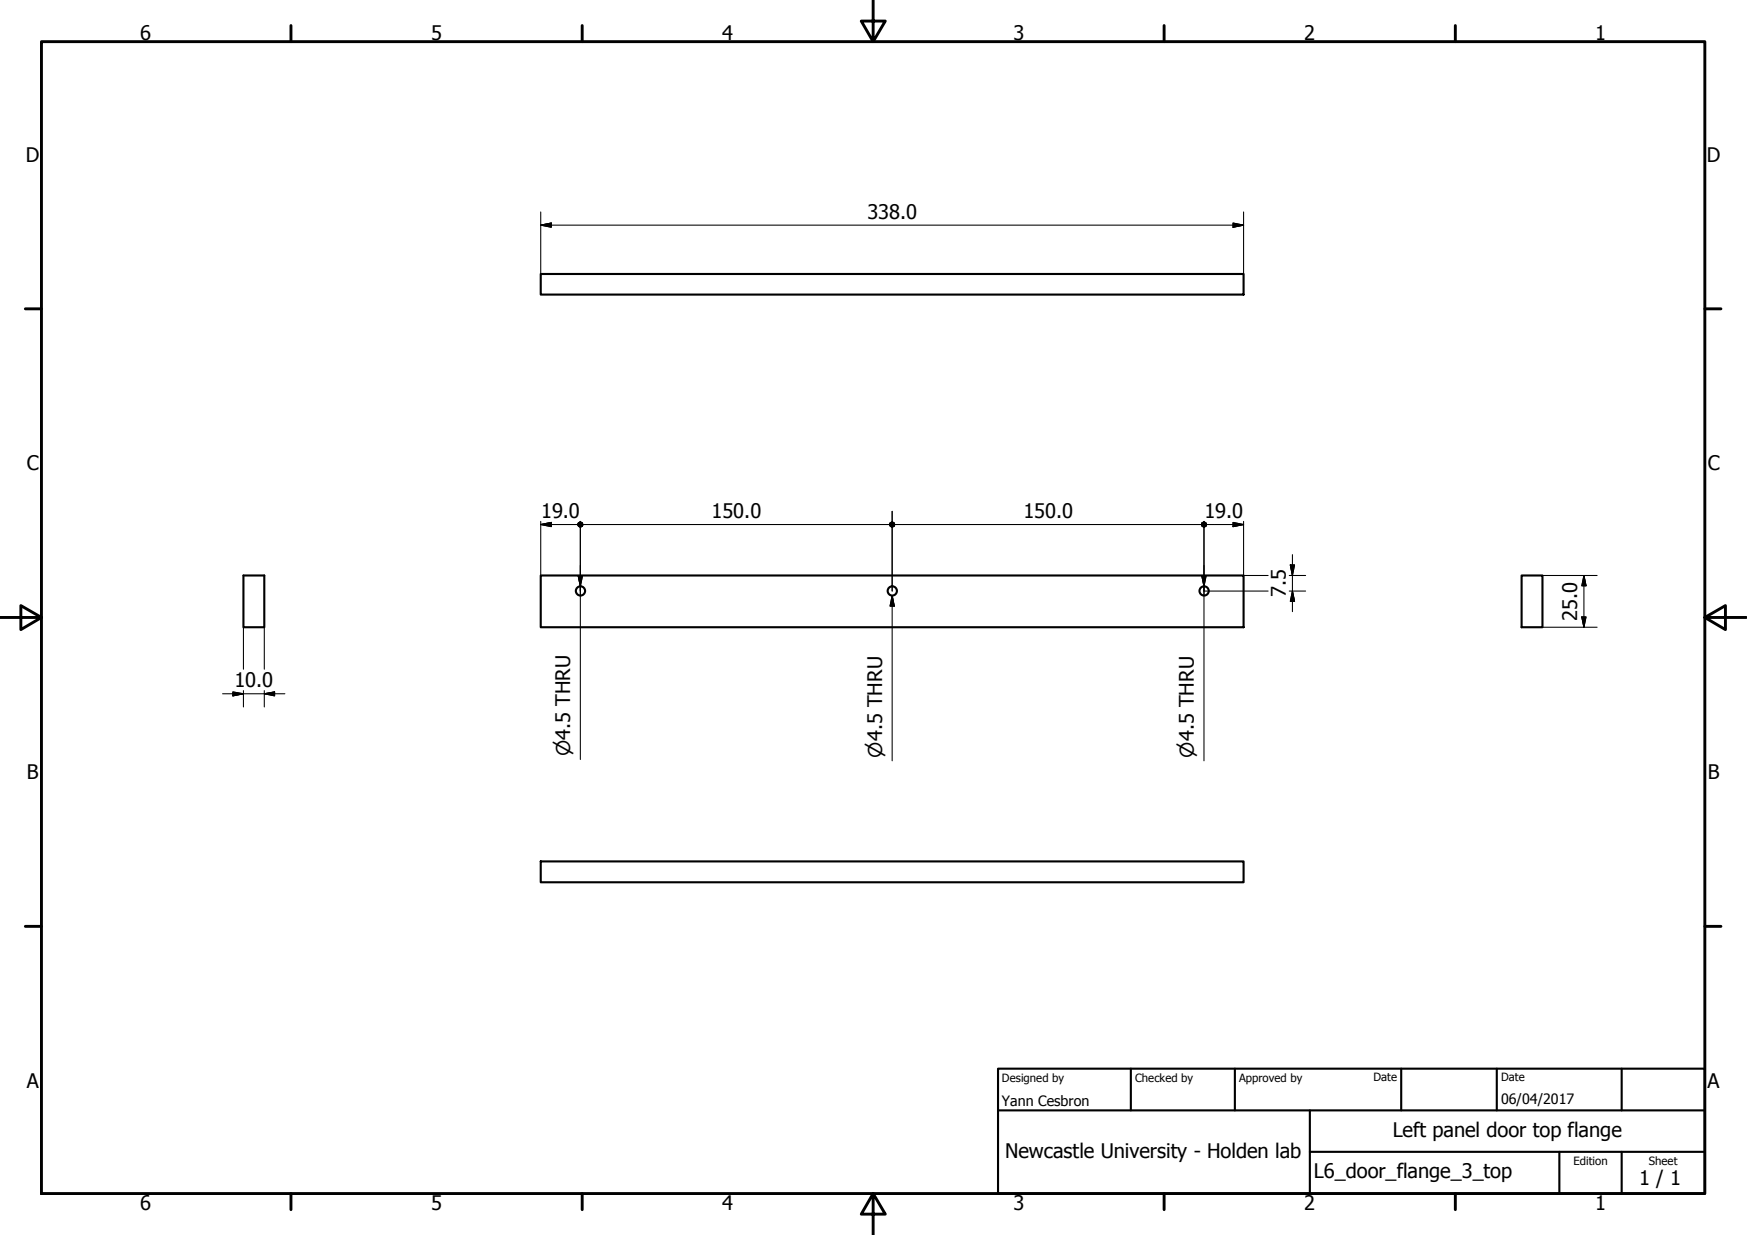
[picture p35: page 1]
L6_door_flange_3_top; Yann Cesbron; Designed by; Checked by; Approved by; Date; Edition; Sheet

Left panel door top flange

Newcastle University - Holden lab
