HoldenLab/microscope-incubation-box/Individual_parts/PDFs/L7_door_flange_4_right.pdf

P

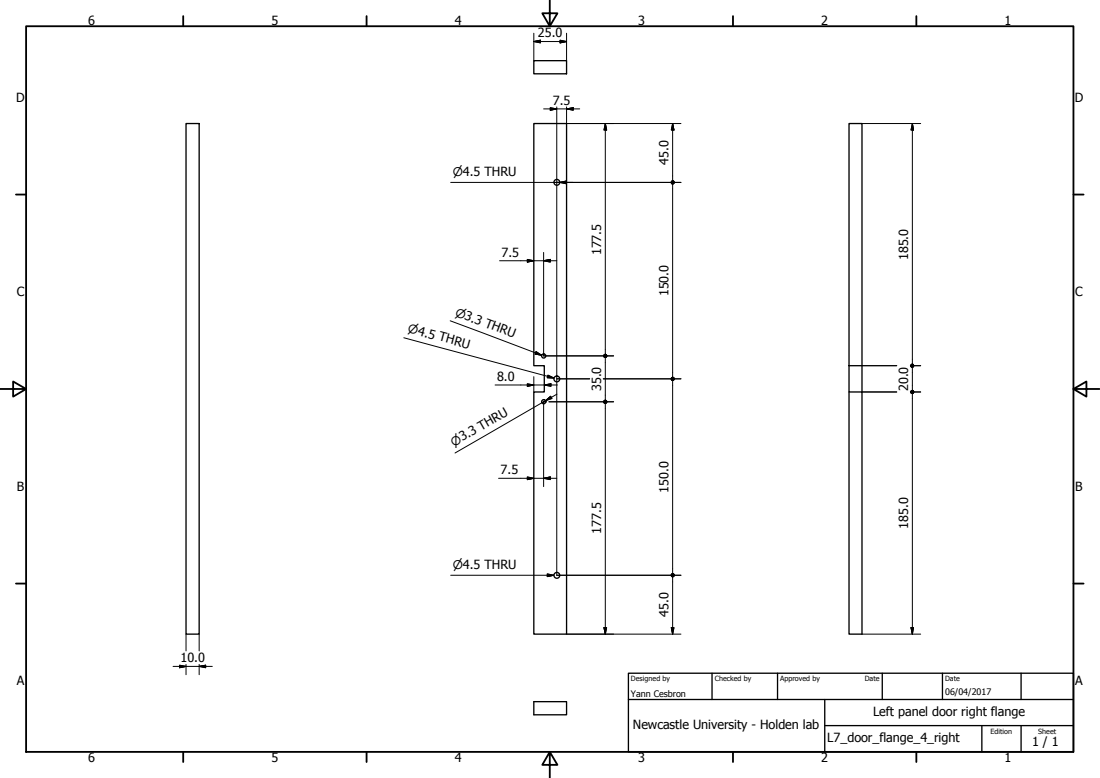
[picture p36: page 1]
fla; tle; old; .3 THRU; P3. 3 THRU; THRU
