HoldenLab/microscope-incubation-box/Individual_parts/PDFs/R1_main.pdf

P

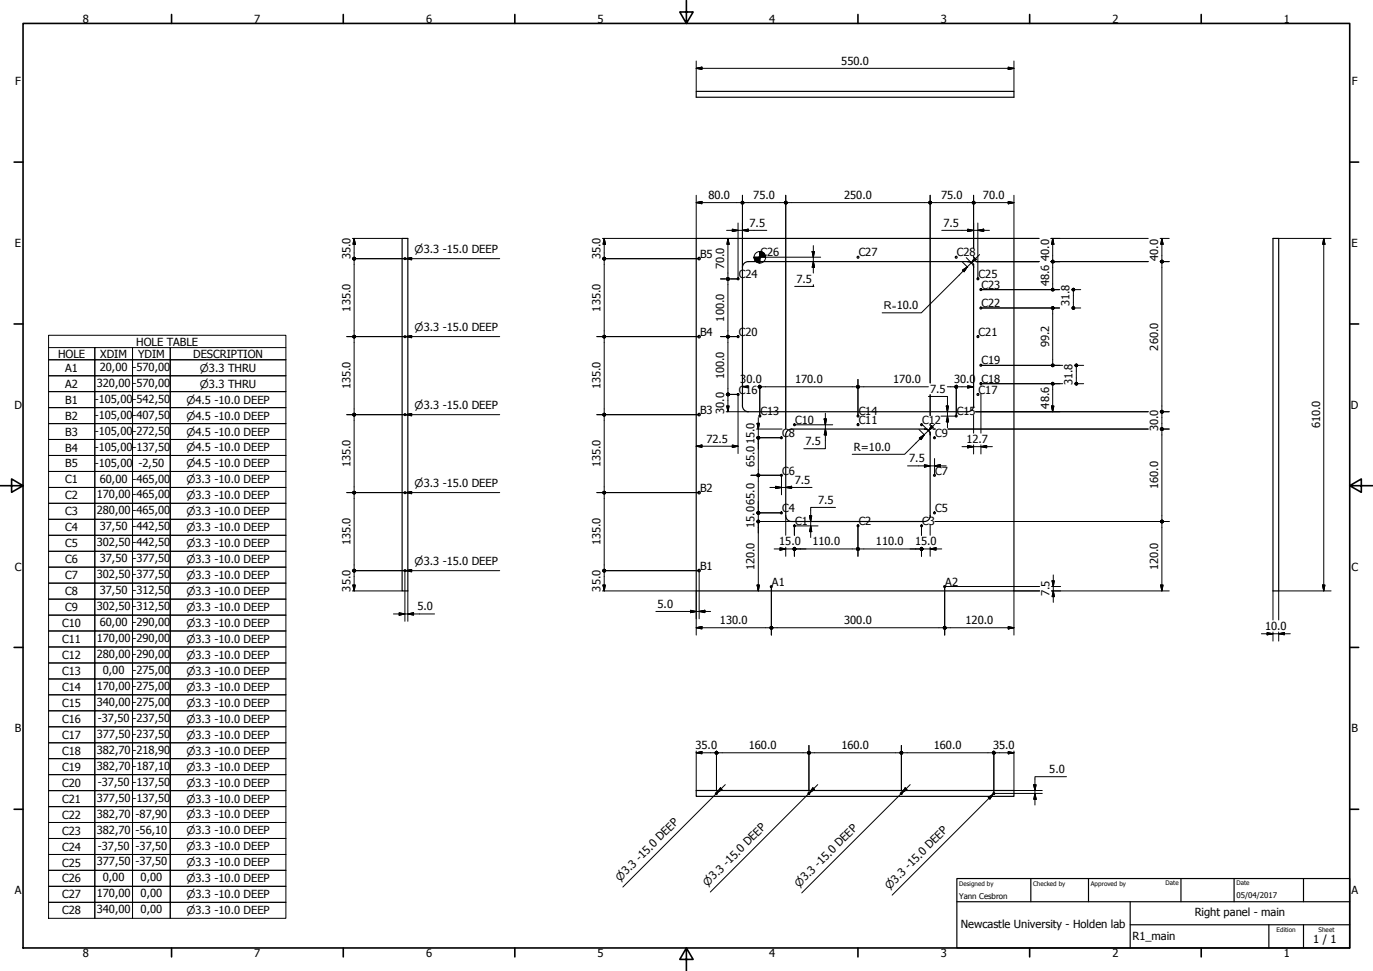
[picture p37: page 1]
tle; old; -15.0 DEEP; .0 DEEP
