HoldenLab/microscope-incubation-box/Individual_parts/PDFs/R2_door.pdf

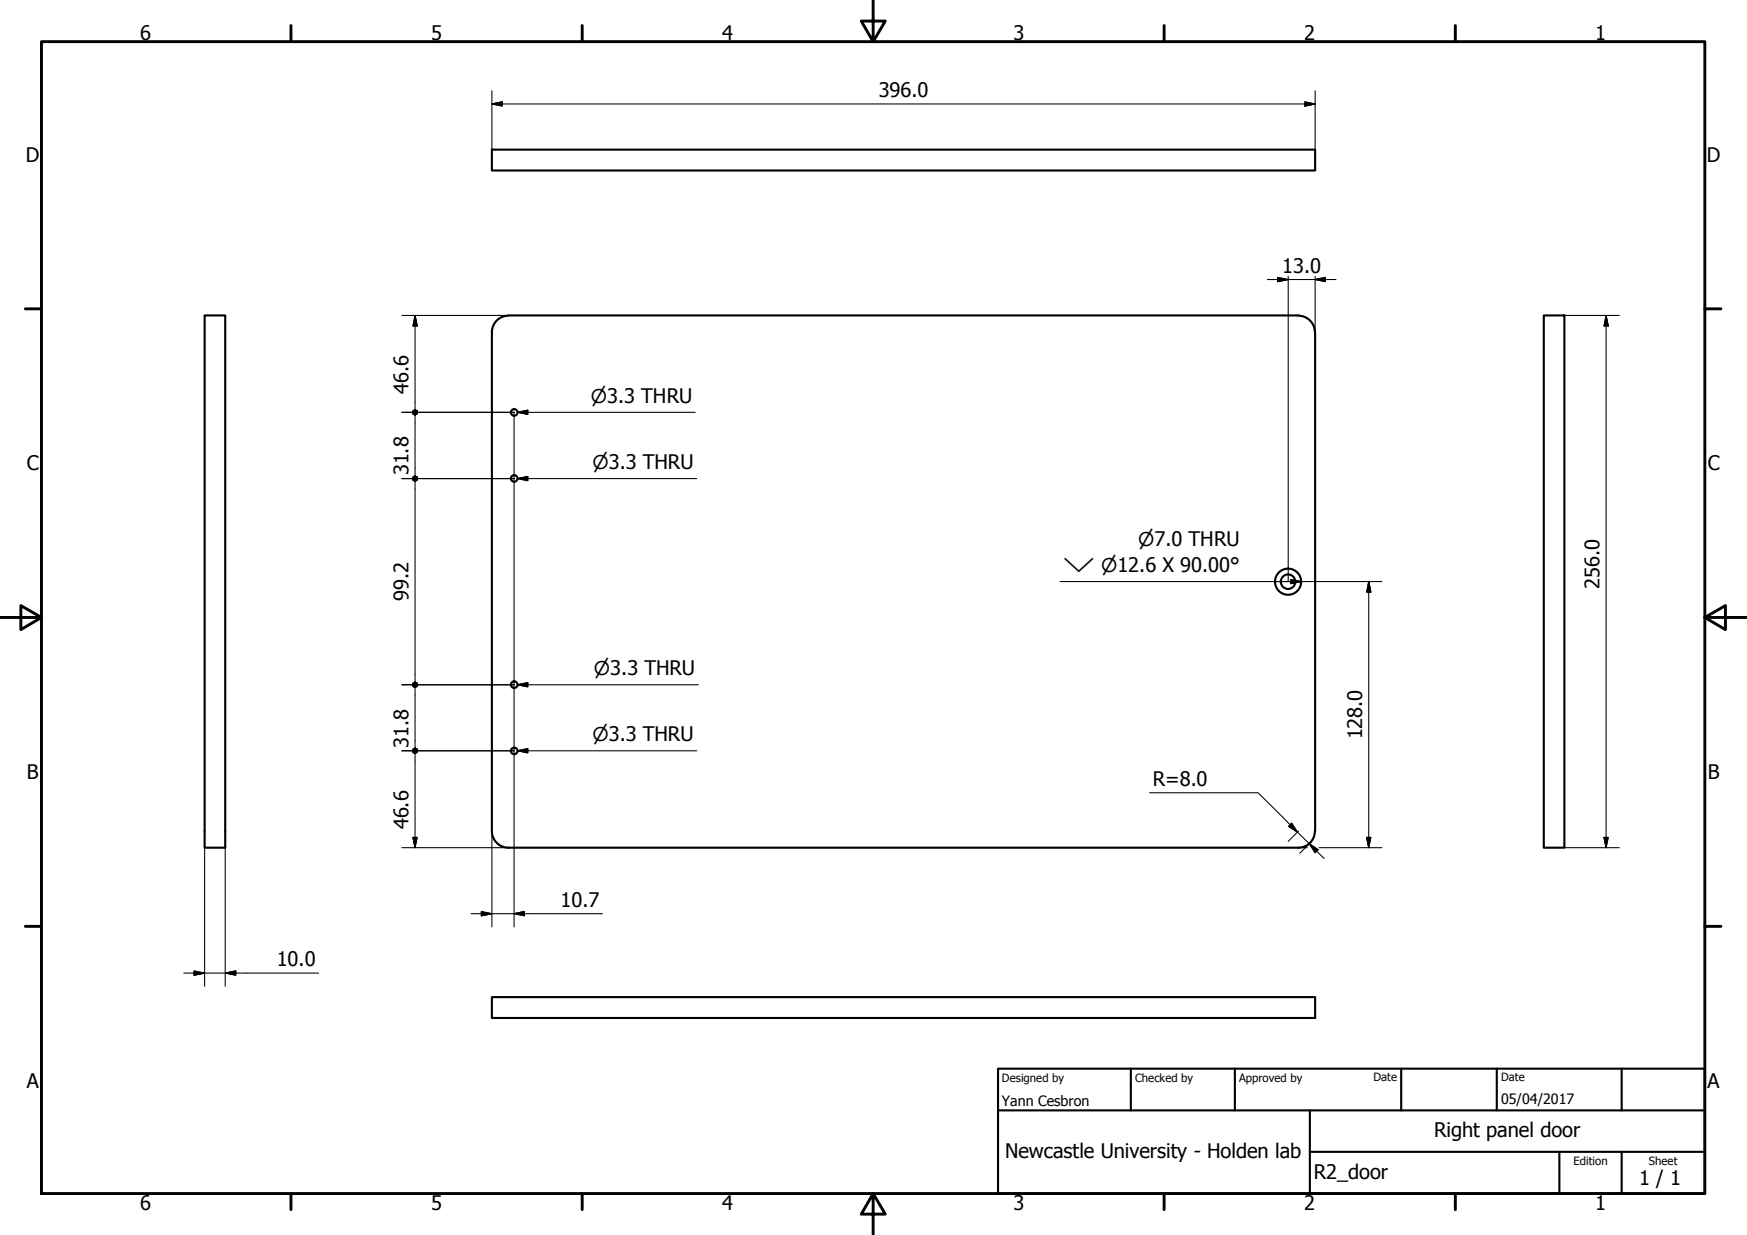
[picture p38: page 1]
R2_door; Yann Cesbron; Designed by; Checked by; Approved by; Date; Edition; Sheet; P7.0 THRU Y P12.6 X 90.00°; P3.3 THRU

Right panel door

Newcastle University - Holden lab
