HoldenLab/microscope-incubation-box/Individual_parts/PDFs/R4_door_flange_right_1.pdf

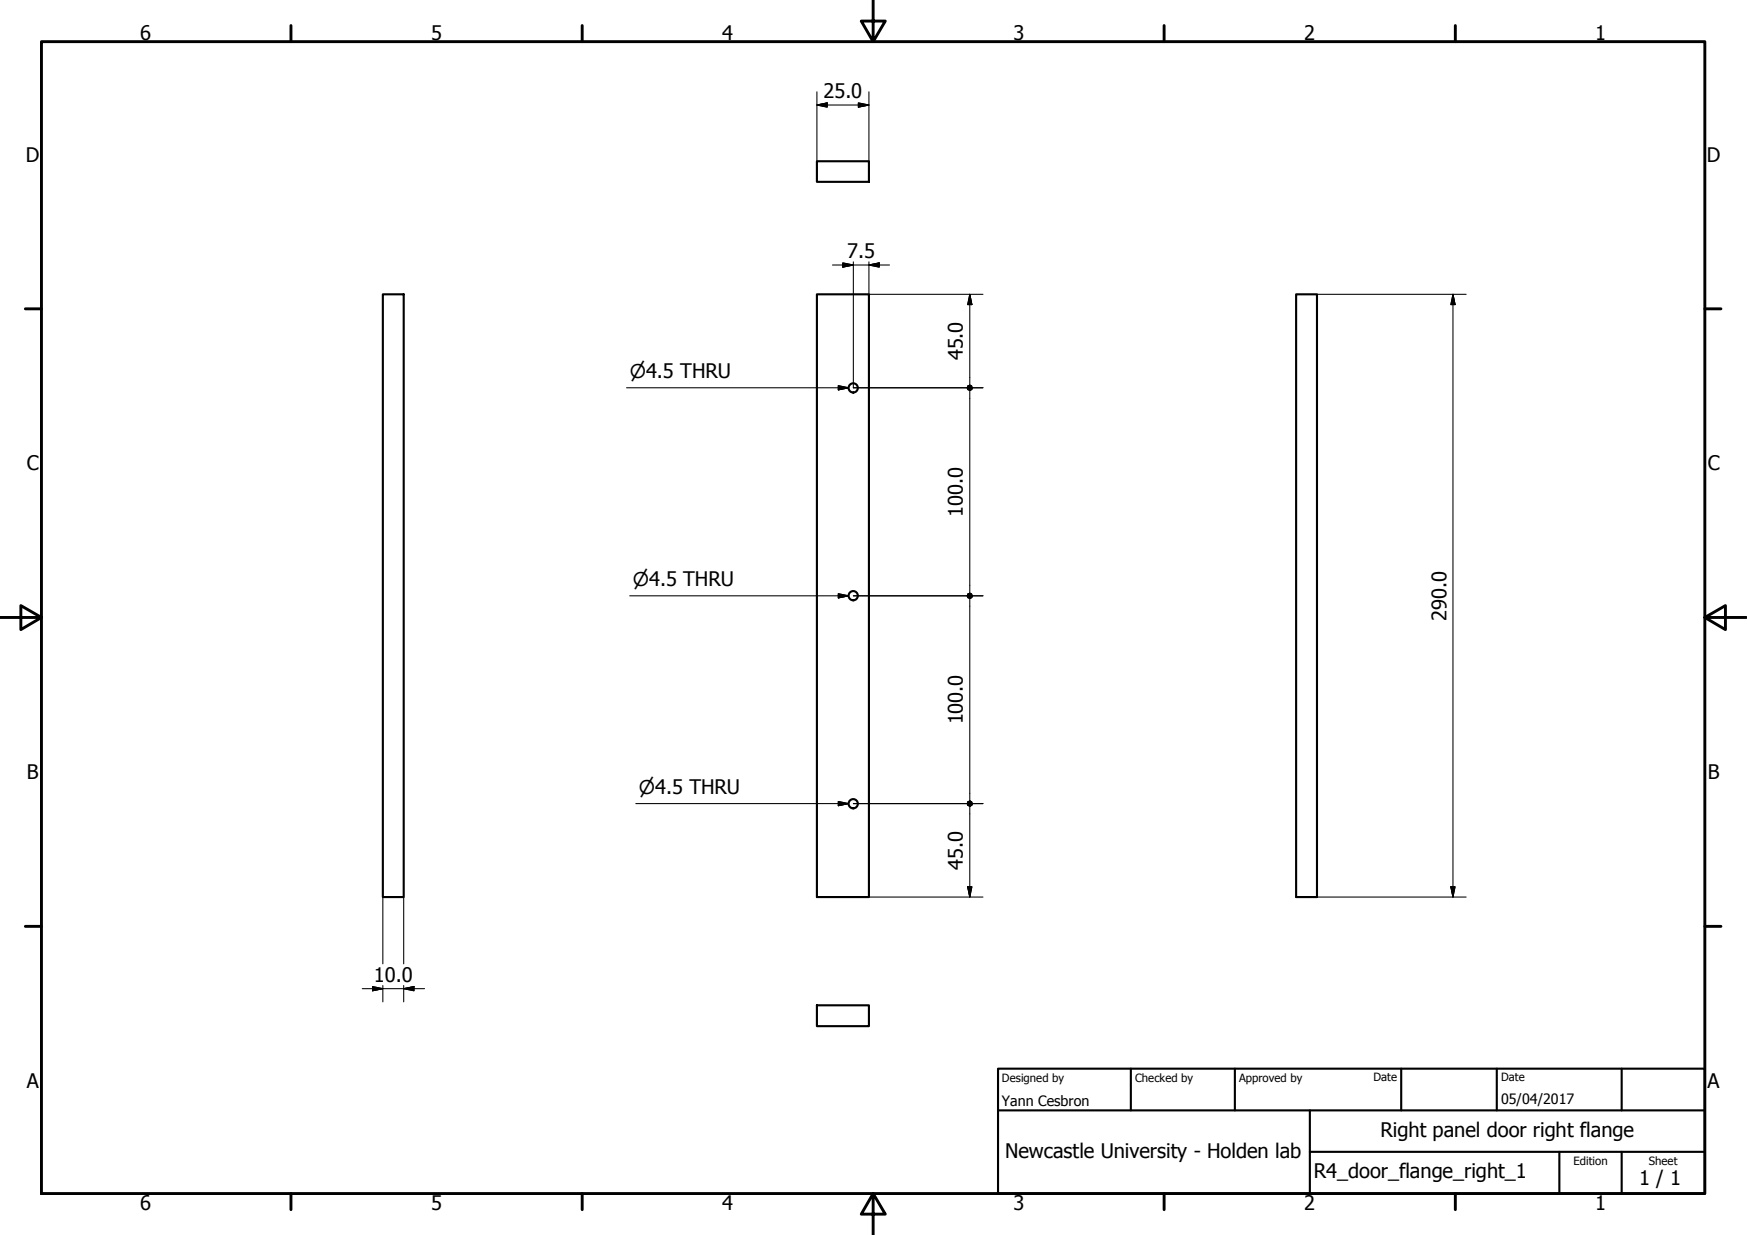
[picture p39: page 1]
R4_door_flange_right_1; Yann Cesbron; Designed by; Checked by; Approved by; Date; Edition; Sheet; P4.5 THRU

Right panel door right flange

Newcastle University - Holden lab
