HoldenLab/microscope-incubation-box/Individual_parts/PDFs/R5_door_flange_top_2.pdf

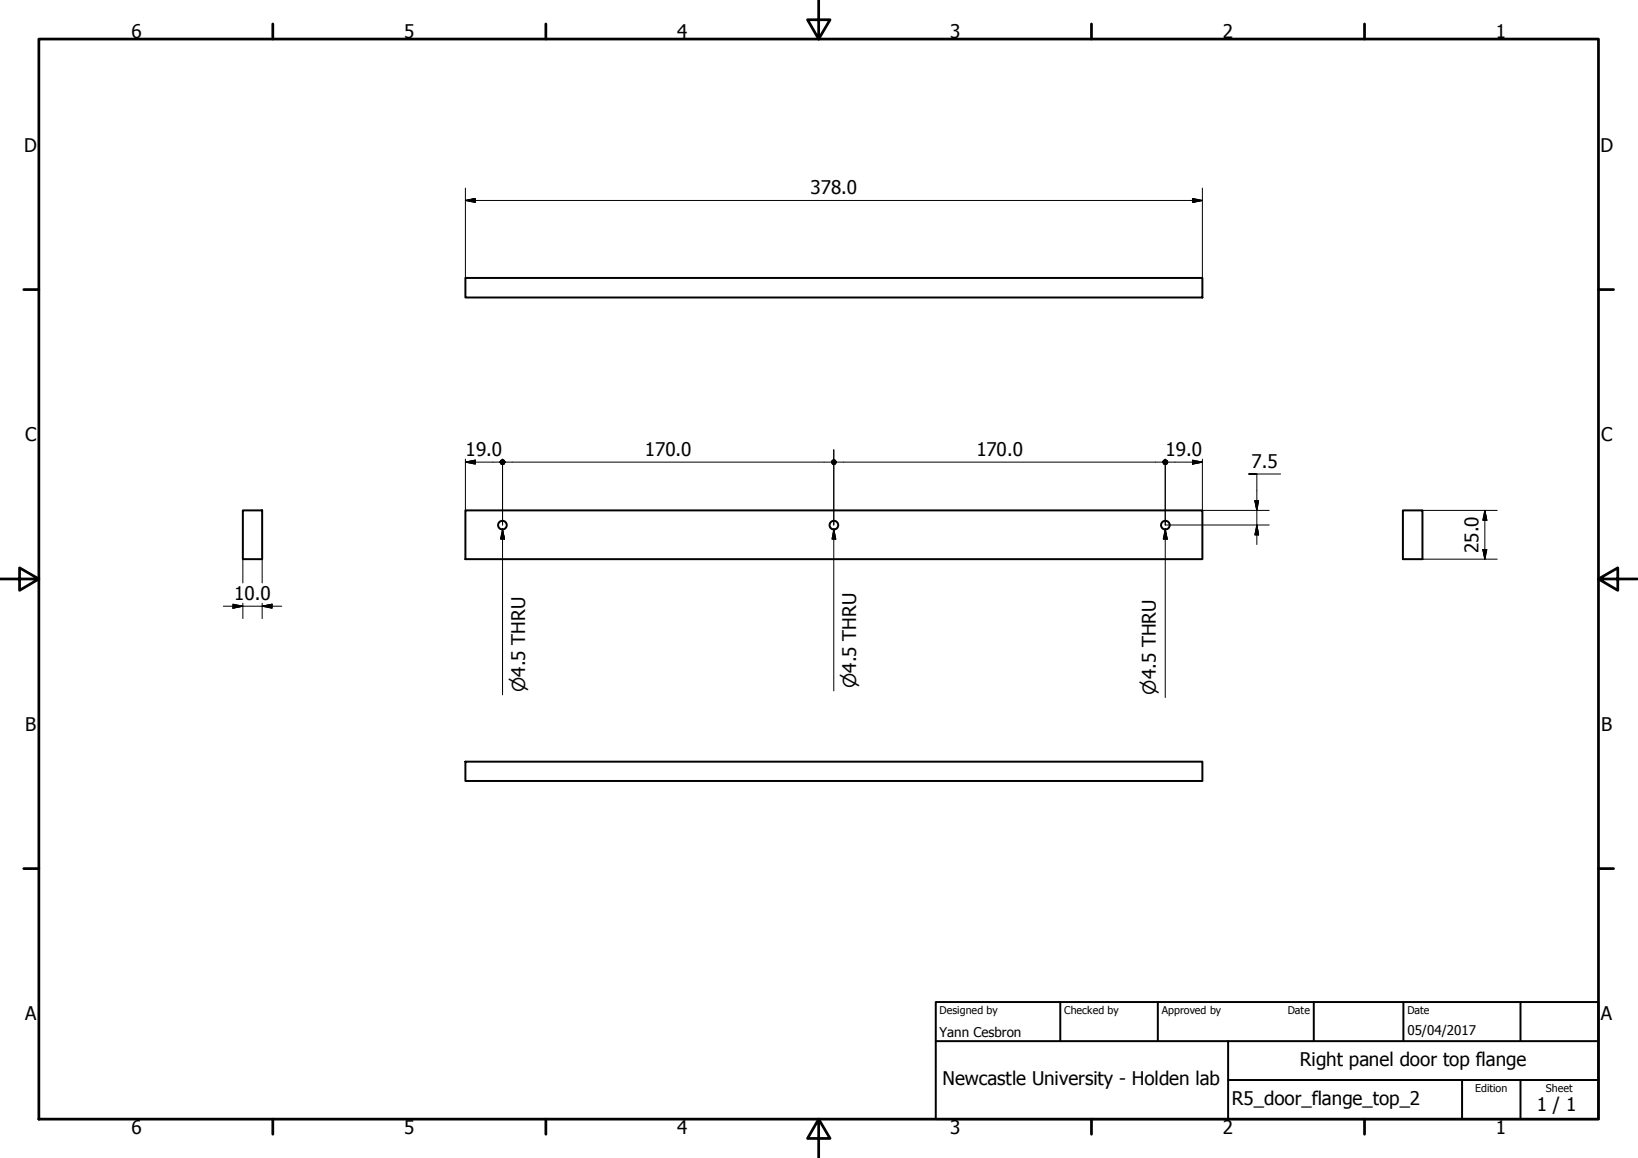
[picture p40: page 1]
R5_door_flange_top_2; Yann Cesbron; Designed by; Checked by; Approved by; Date; Edition; Sheet

Right panel door top flange

Newcastle University - Holden lab
