HoldenLab/microscope-incubation-box/Individual_parts/PDFs/R6_door_flange_bottom_3.pdf

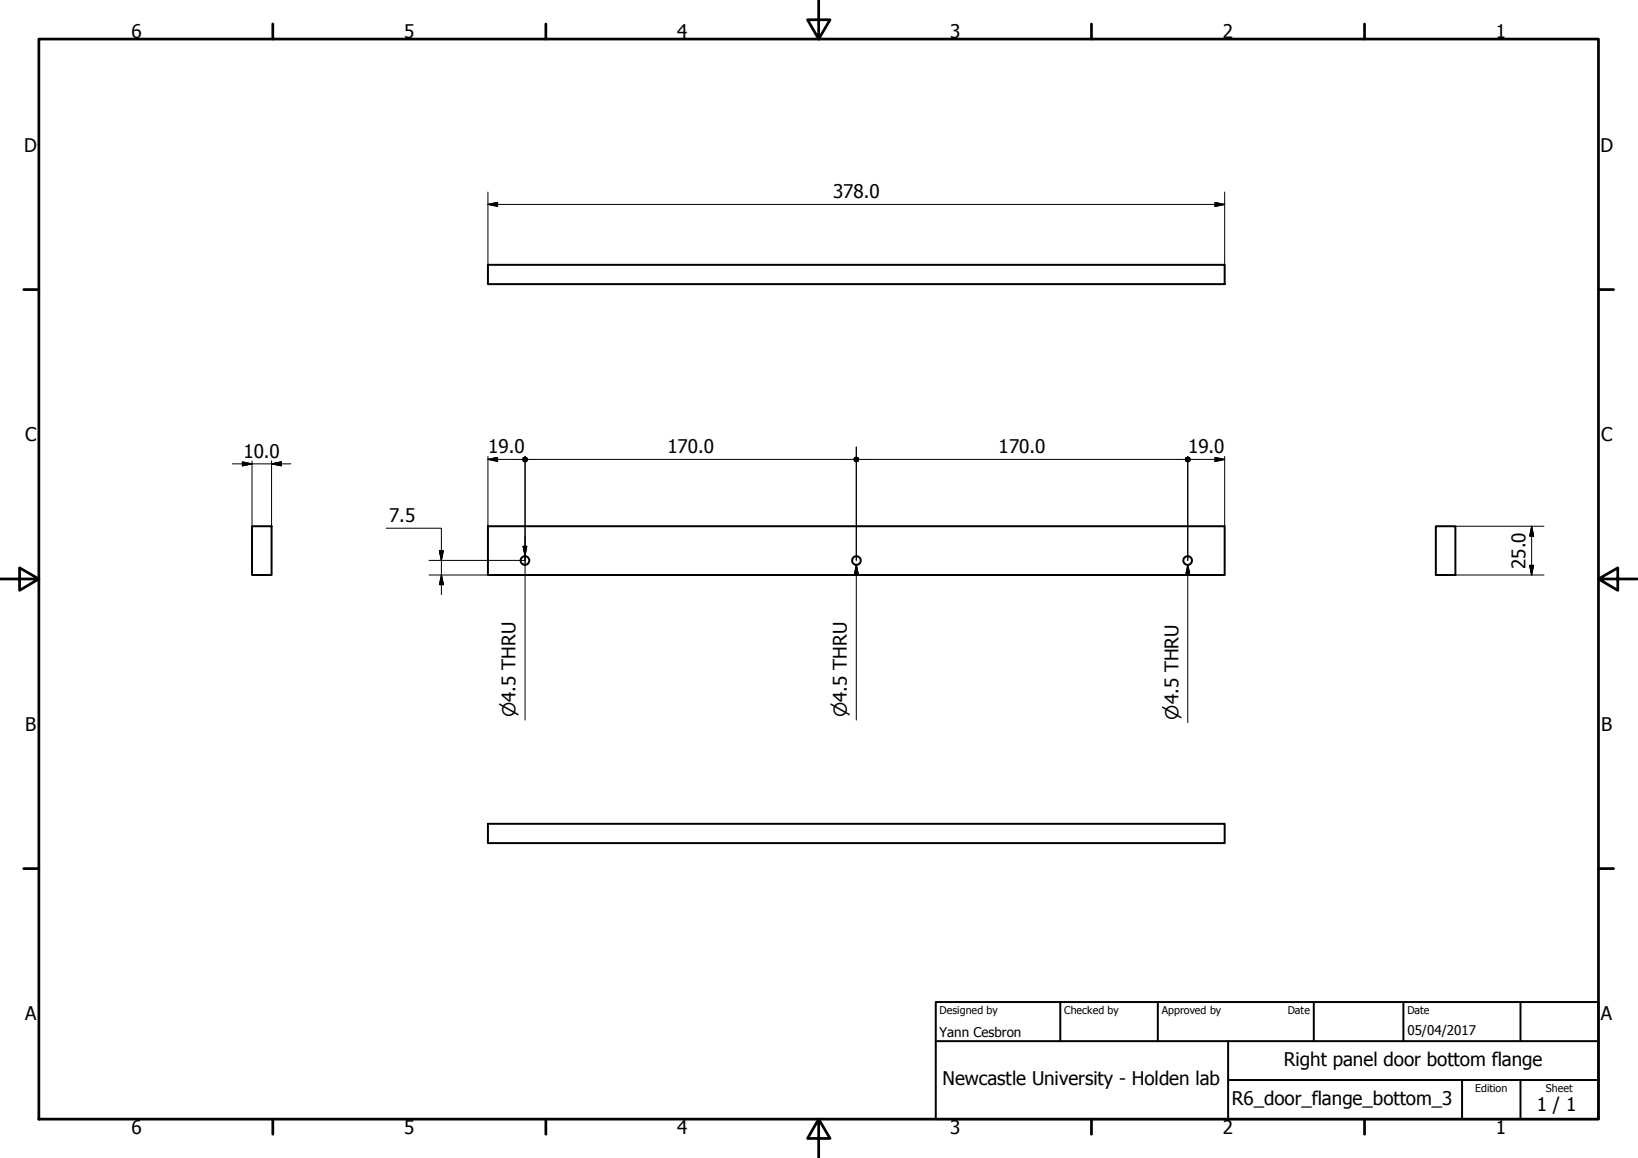
[picture p41: page 1]
R6_door_flange_bottom_3; Yann Cesbron; Designed by; Checked by; Approved by; Date; Edition; Sheet

Right panel door bottom flange

Newcastle University - Holden lab
