HoldenLab/microscope-incubation-box/Individual_parts/PDFs/R7_door_flange_left_4.pdf

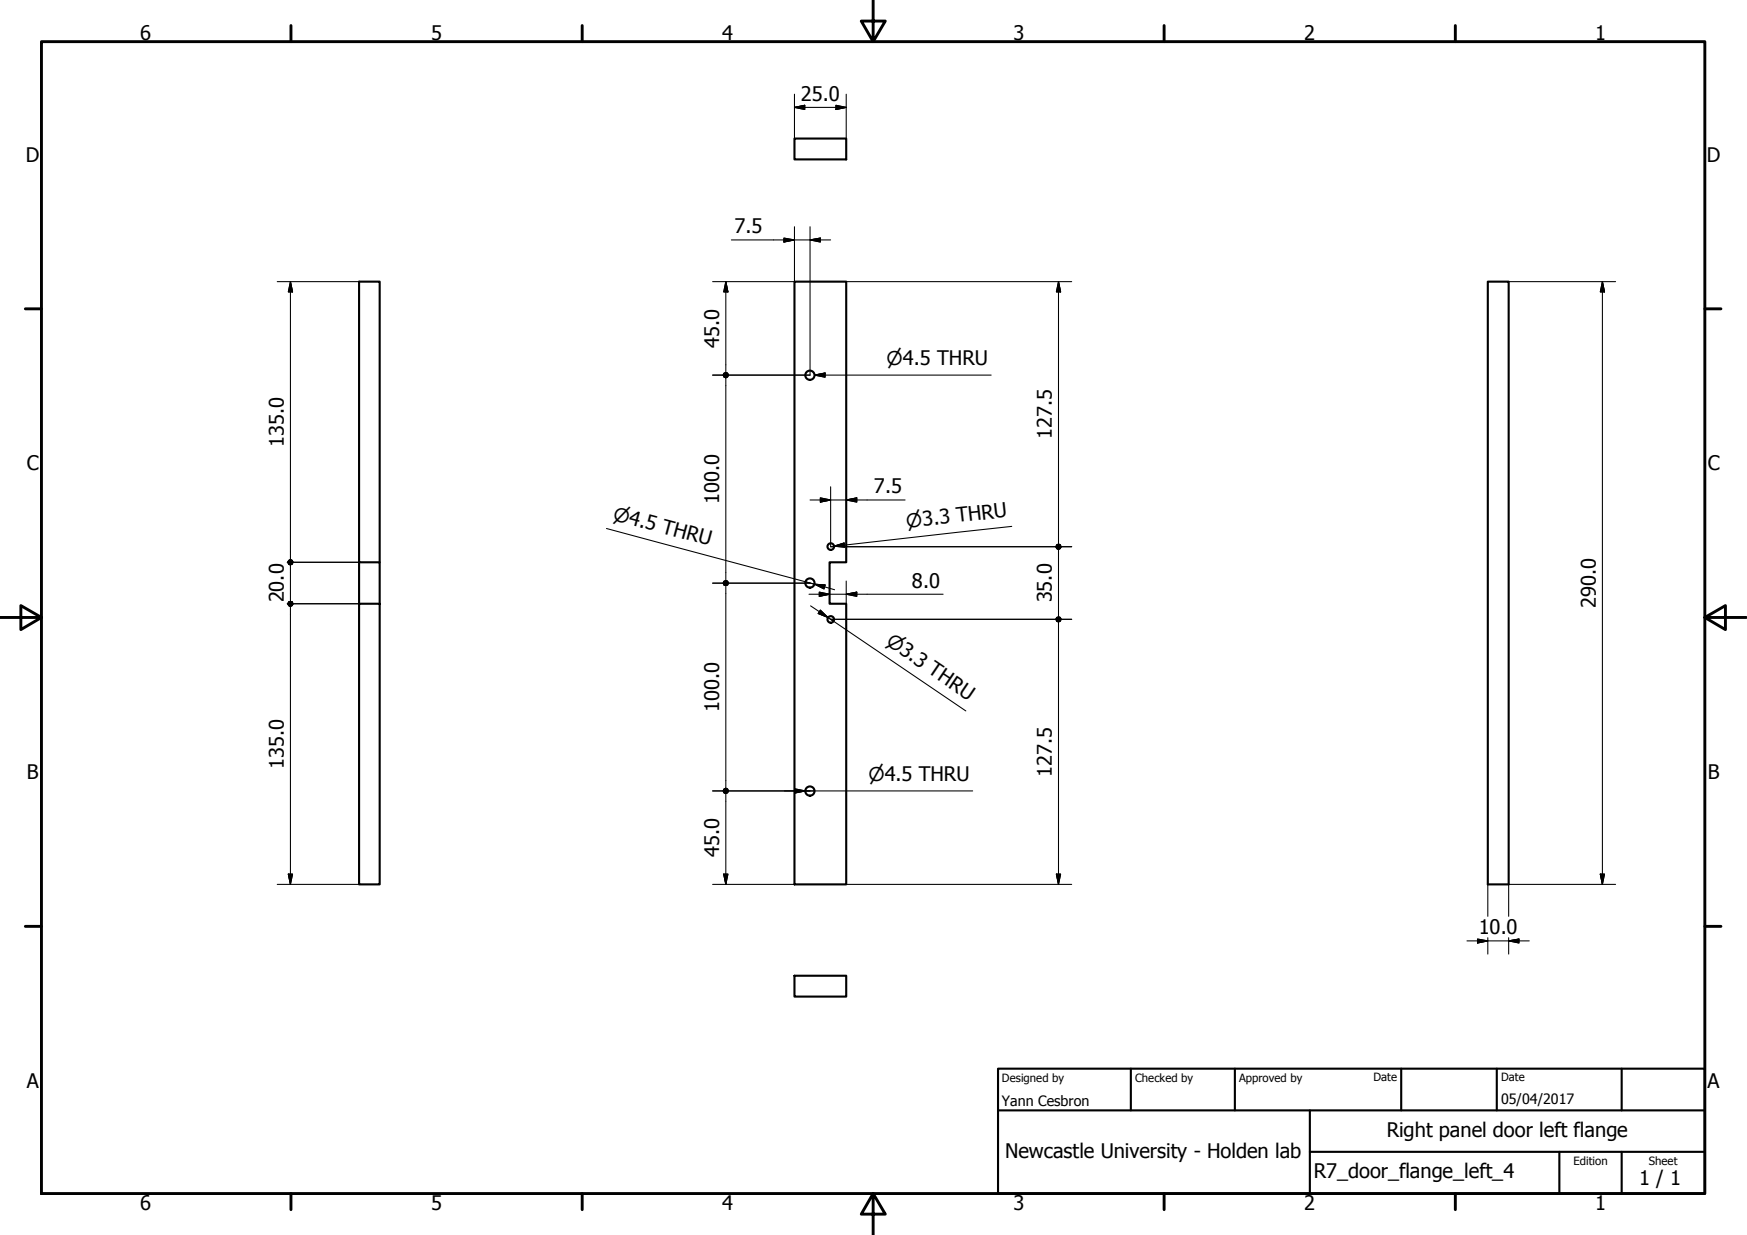
[picture p42: page 1]
R7_door_flange_left_4; Yann Cesbron; Designed by; Checked by; Approved by; Date; Edition; Sheet; P4.5 THRU; P3.3 THRU

Right panel door left flange

Newcastle University - Holden lab
