HoldenLab/microscope-incubation-box/Individual_parts/PDFs/T1_main.pdf

P
P

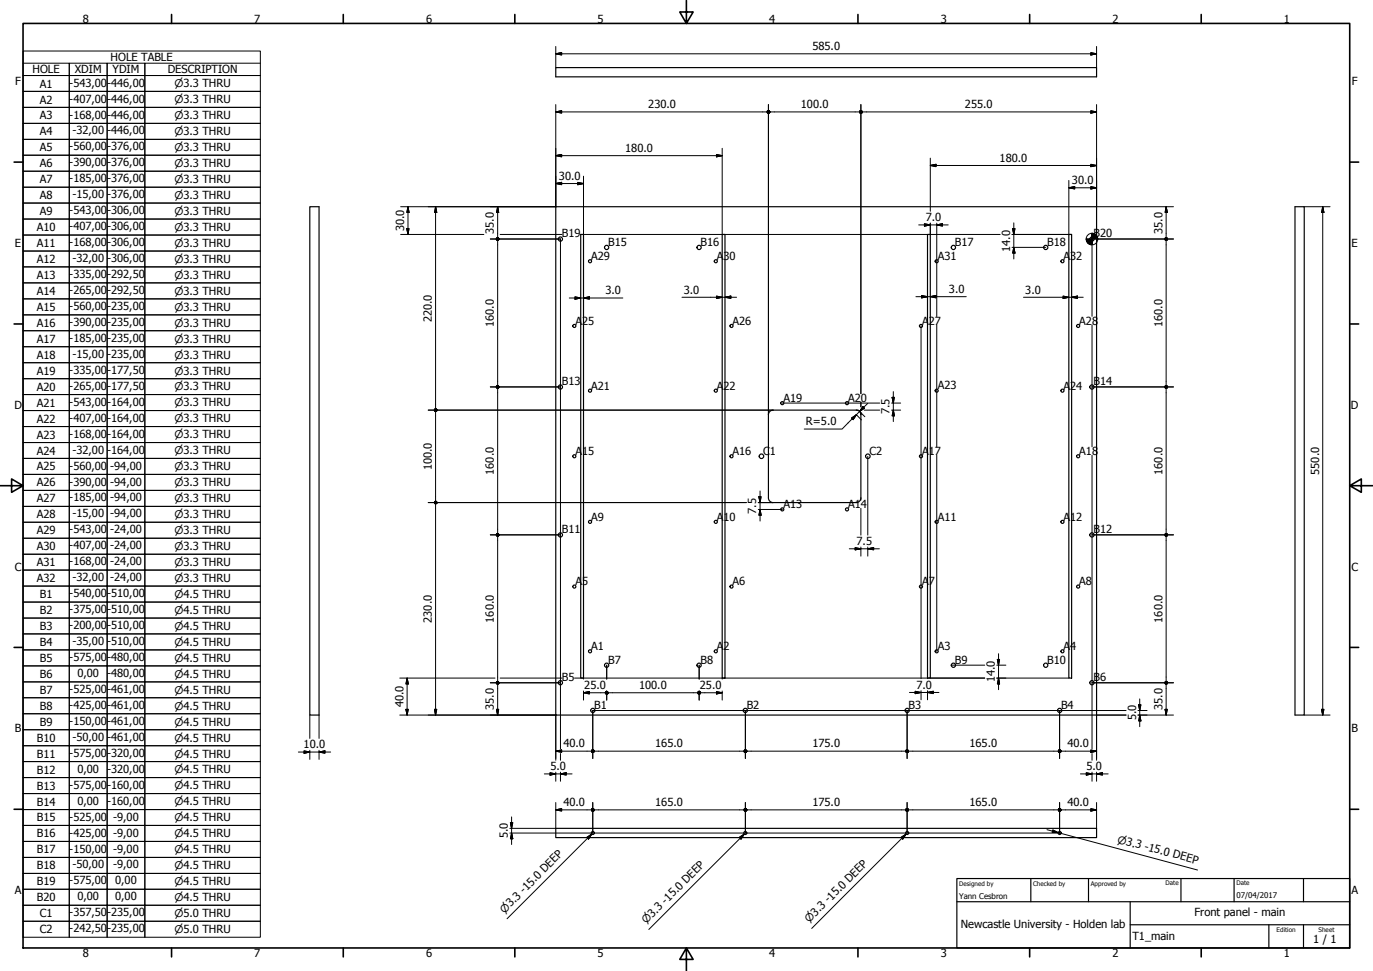
[picture p43: page 1]
tle; old; -15.0 DEEP; DEEP
