HoldenLab/microscope-incubation-box/Individual_parts/PDFs/T2_cover.pdf

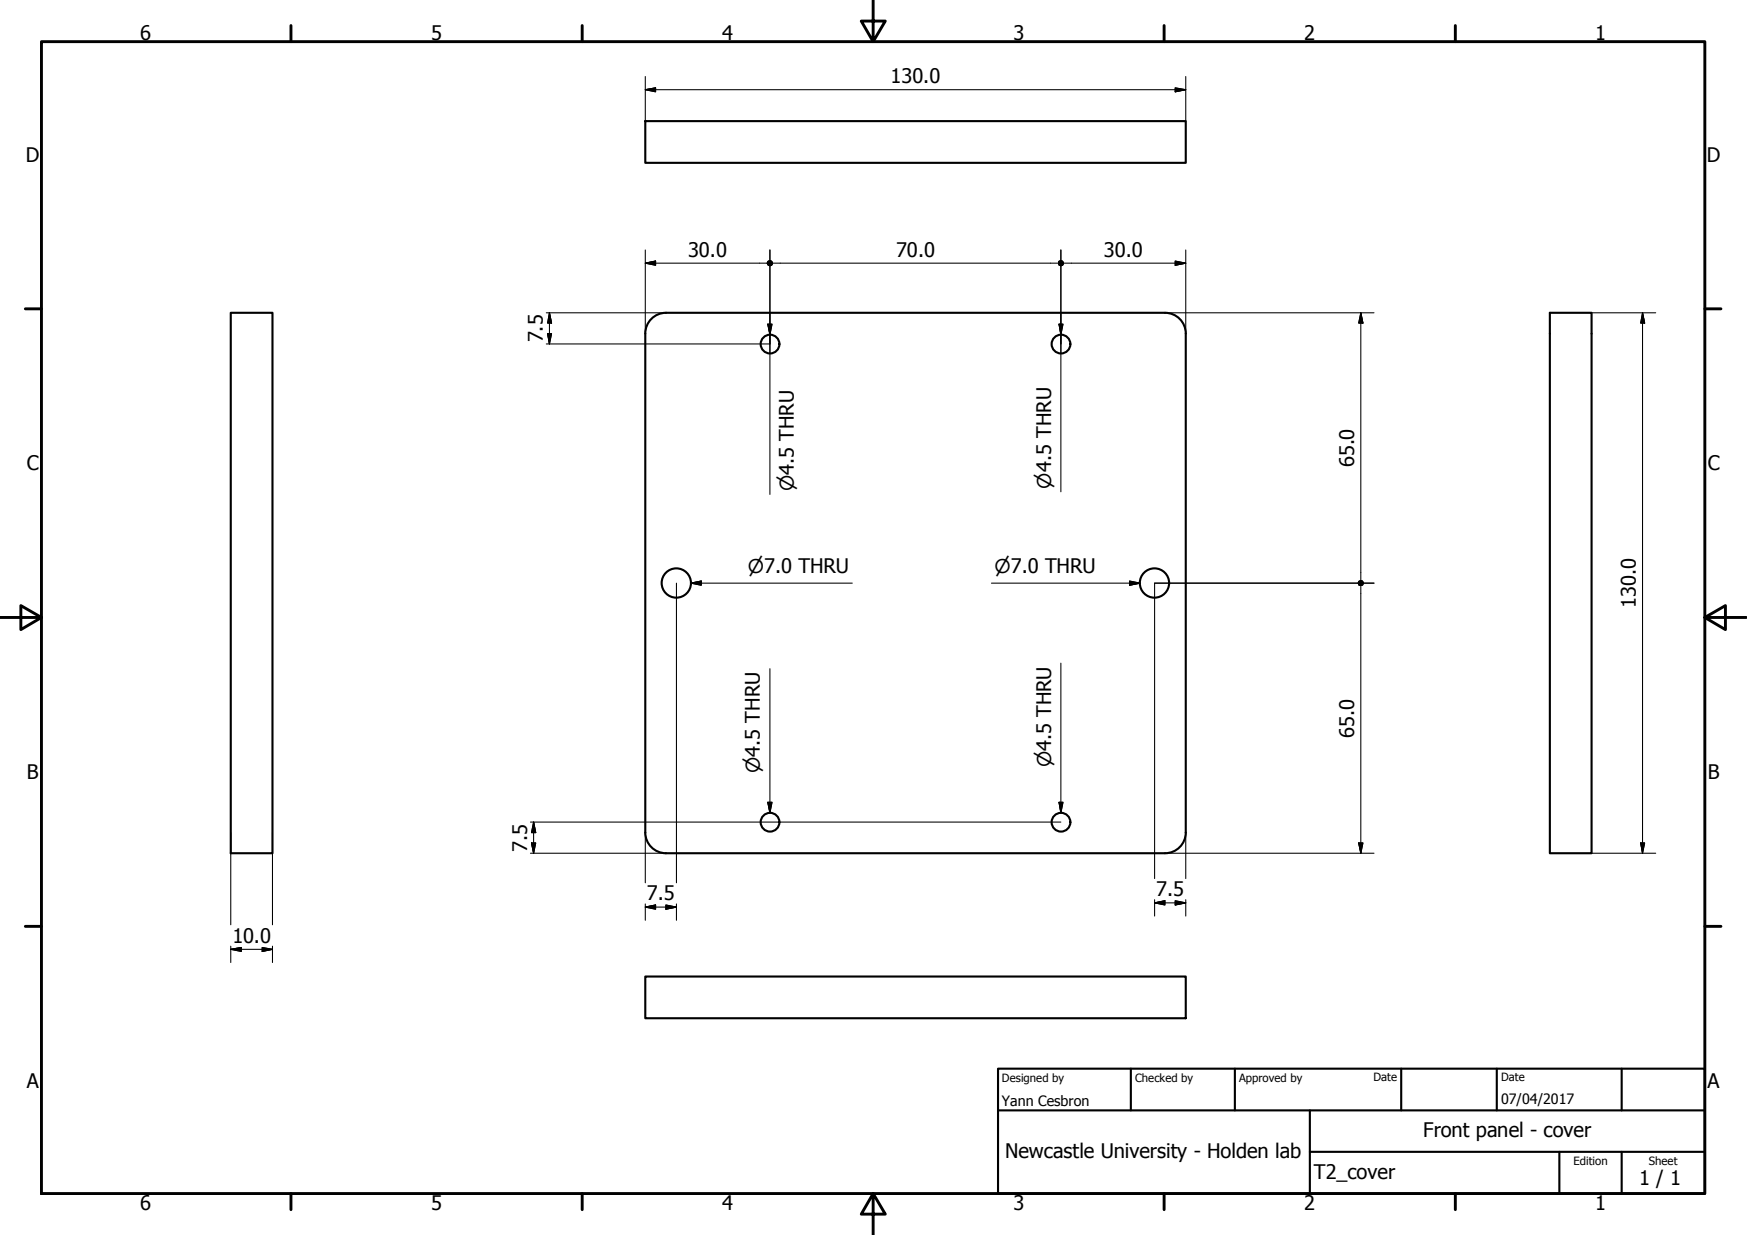
[picture p44: page 1]
T2_cover; Yann Cesbron; Designed by; Checked by; Approved by; Date; Edition; Sheet; P7.0 THRU

Front panel - cover

Newcastle University - Holden lab
