HoldenLab/microscope-incubation-box/Individual_parts/PDFs/Missing_holes/R1_main.pdf

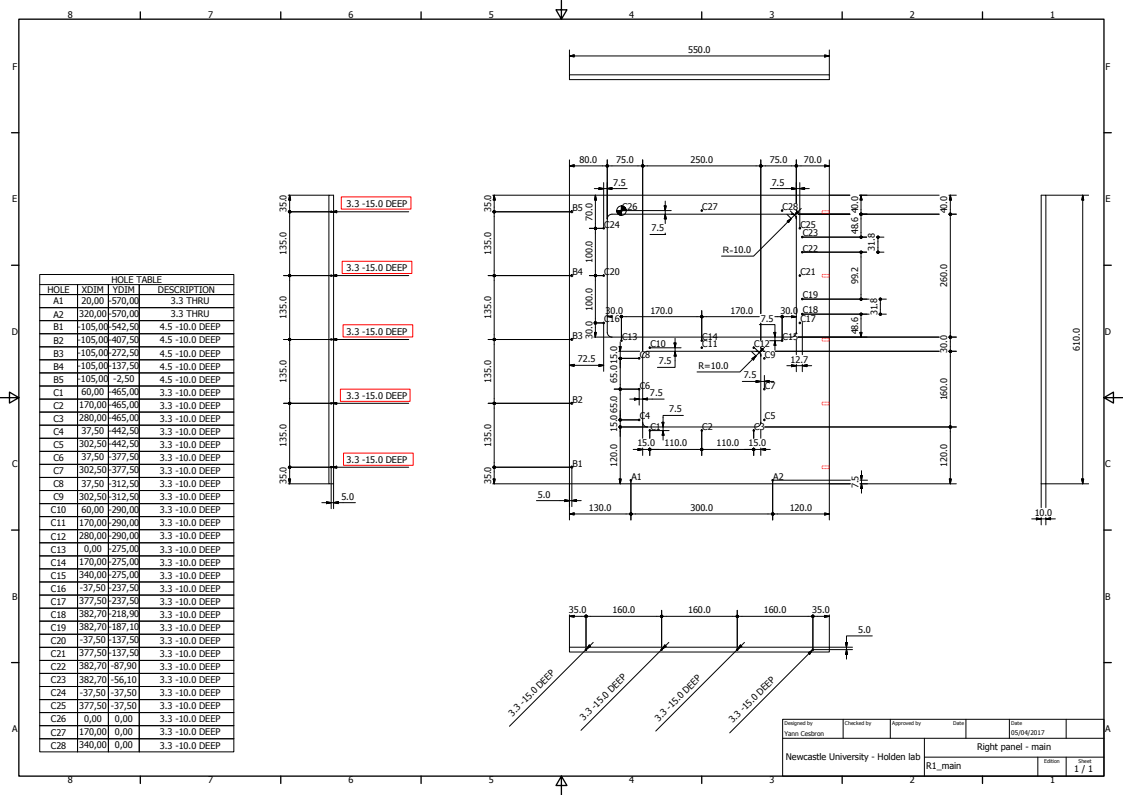
[picture p45: page 1]

Newcastle University - Holden lab
